coelacant1/SigmaProtogen/BetaProtogen/Pictures/20210629_173443.jpg

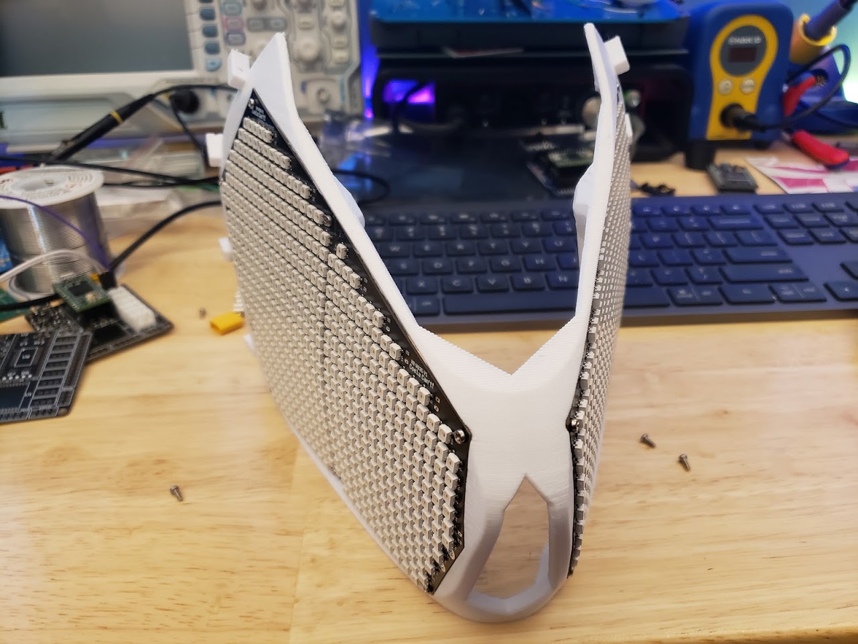
BetaProtogen/Pictures/20210629_173443.jpg
