coelacant1/SigmaProtogen/BetaProtogen/Pictures/BottomLayer.png

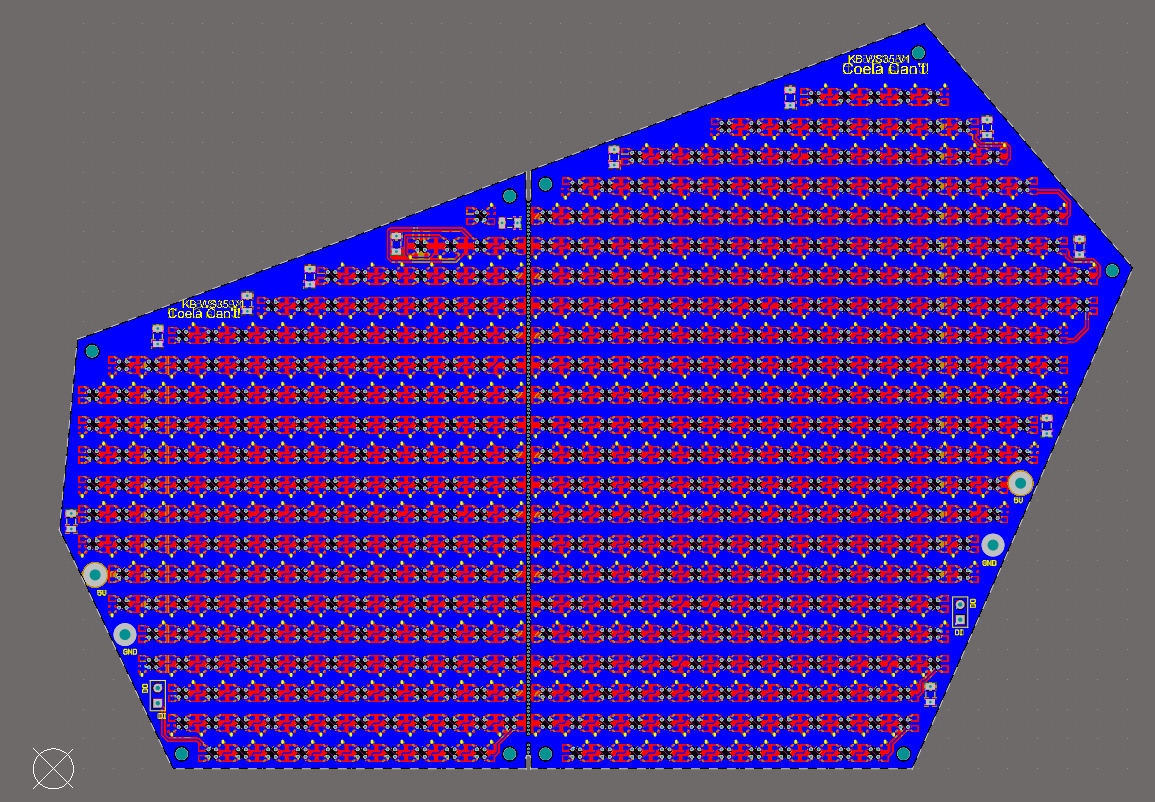
BetaProtogen/Pictures/BottomLayer.png
