coelacant1/SigmaProtogen/BetaProtogen/Pictures/CoelaProtoPublicV1_WS35_blank.png

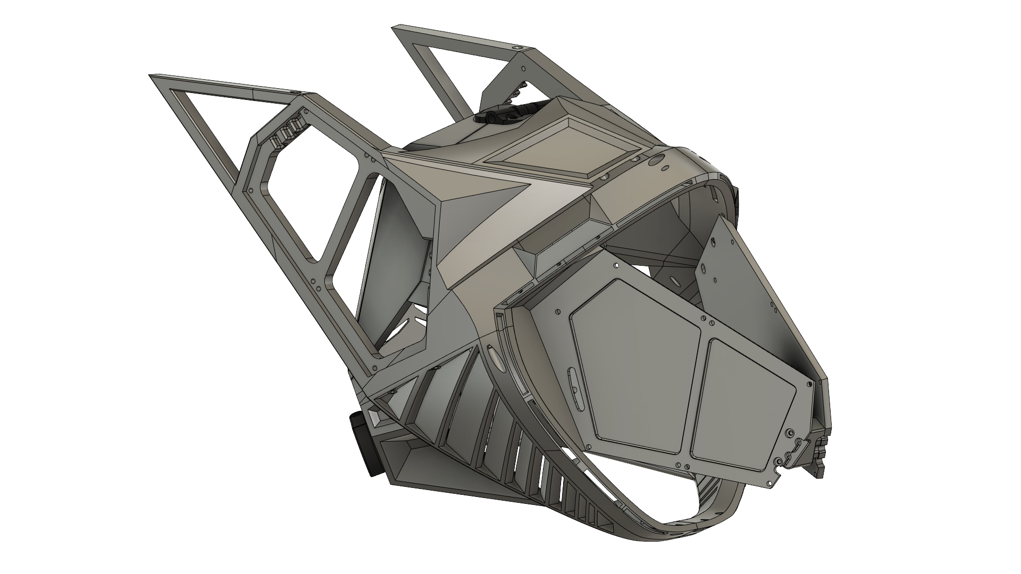
BetaProtogen/Pictures/CoelaProtoPublicV1_WS35_blank.png
