coelacant1/SigmaProtogen/BetaProtogen/Pictures/CoelaProtoPublicV1_WS35_Bottom.png

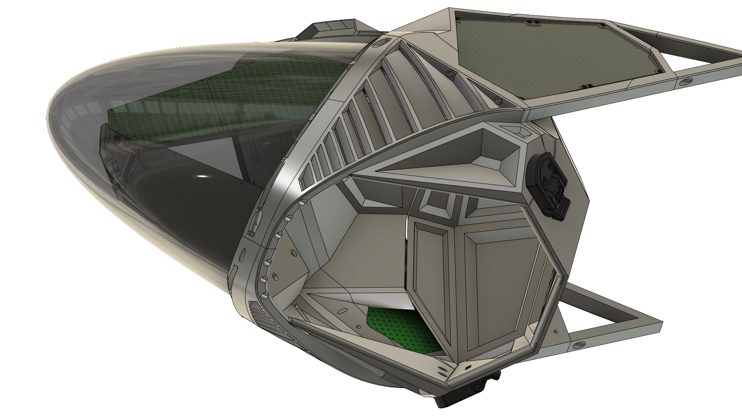
BetaProtogen/Pictures/CoelaProtoPublicV1_WS35_Bottom.png
