coelacant1/SigmaProtogen/BetaProtogen/Pictures/CoelaProtoPublicV1_WS35_Full.png

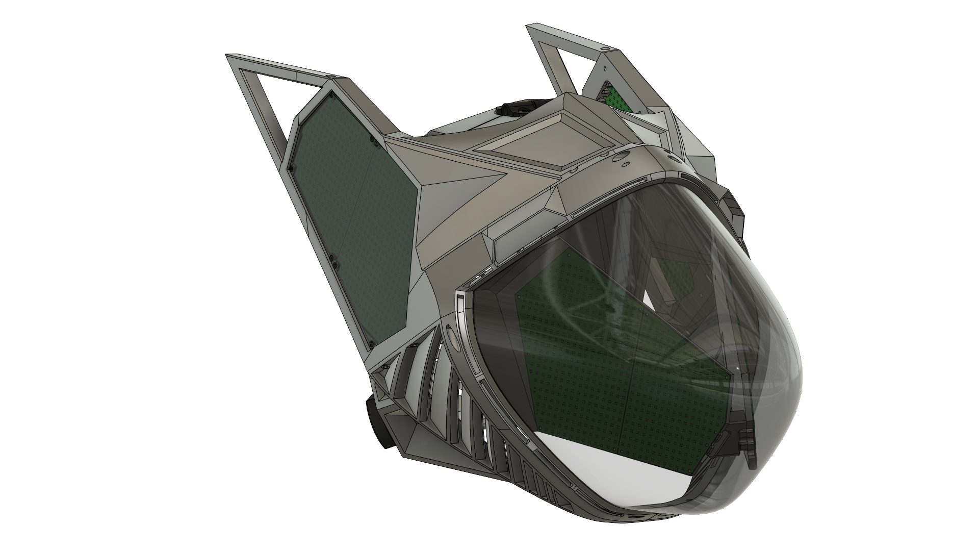
BetaProtogen/Pictures/CoelaProtoPublicV1_WS35_Full.png
