coelacant1/SigmaProtogen/BetaProtogen/Pictures/CoelaProtoPublicV1_WS35_Open.png

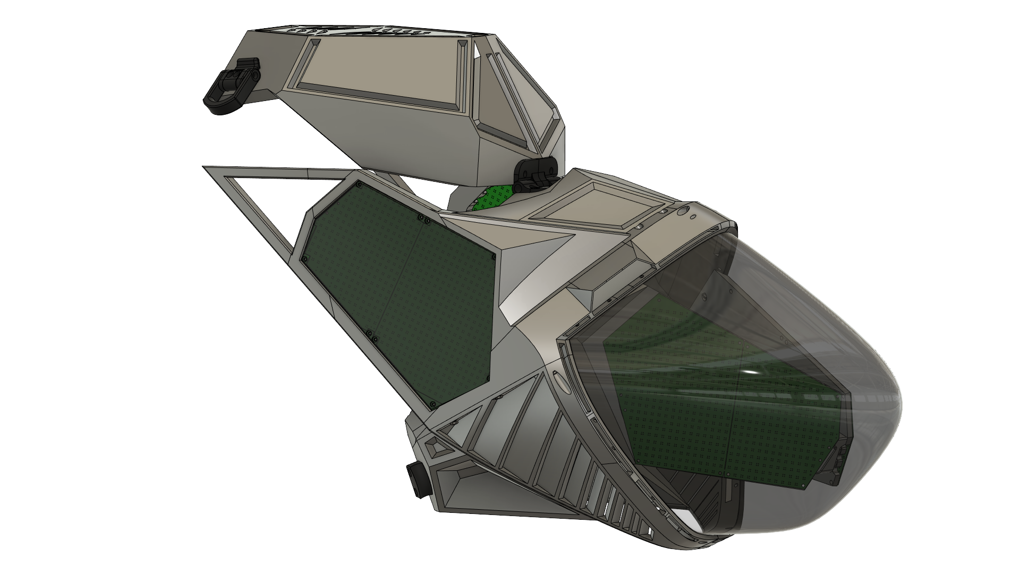
BetaProtogen/Pictures/CoelaProtoPublicV1_WS35_Open.png
