coelacant1/SigmaProtogen/BetaProtogen/Pictures/CoelaProtoPublicV1_WS35_OpenBack.png

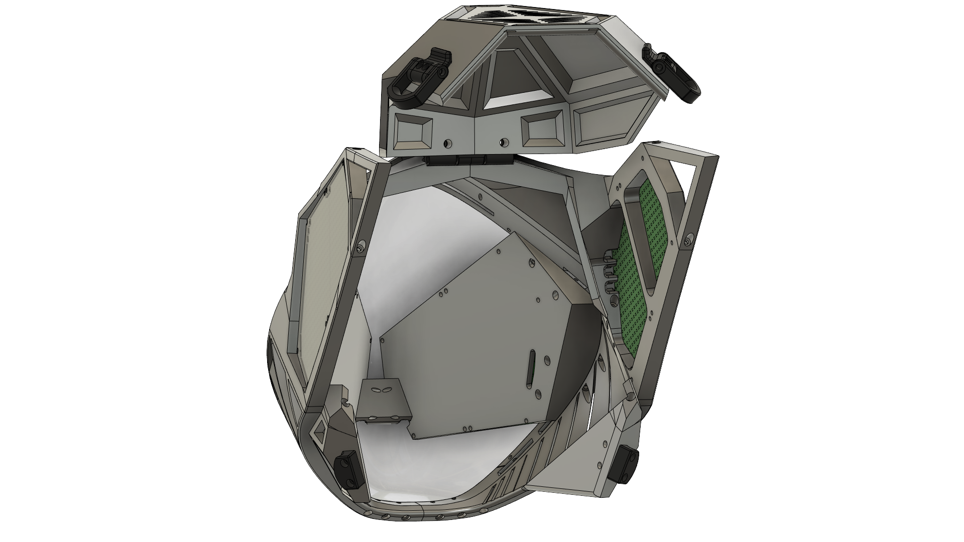
BetaProtogen/Pictures/CoelaProtoPublicV1_WS35_OpenBack.png
