coelacant1/SigmaProtogen/BetaProtogen/Pictures/E_W8pO6XIAAdrPj.jpg

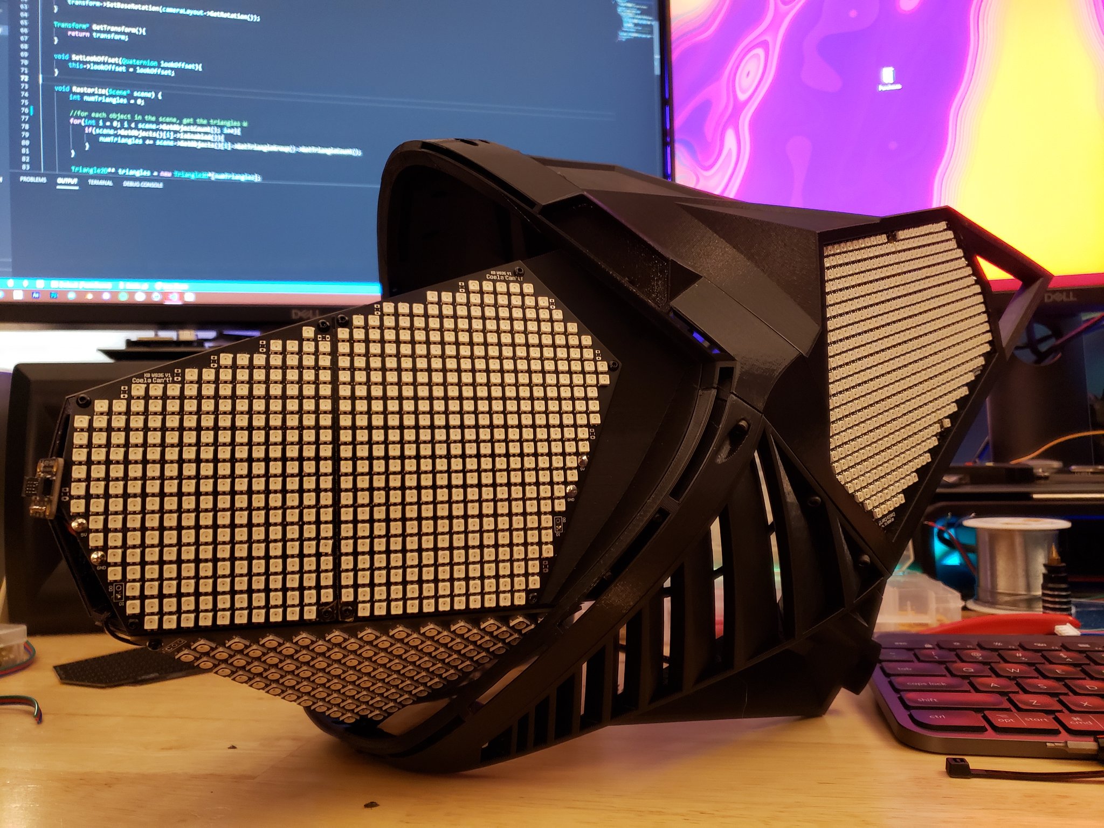
BetaProtogen/Pictures/E_W8pO6XIAAdrPj.jpg
