coelacant1/SigmaProtogen/BetaProtogen/Pictures/FullHead.png

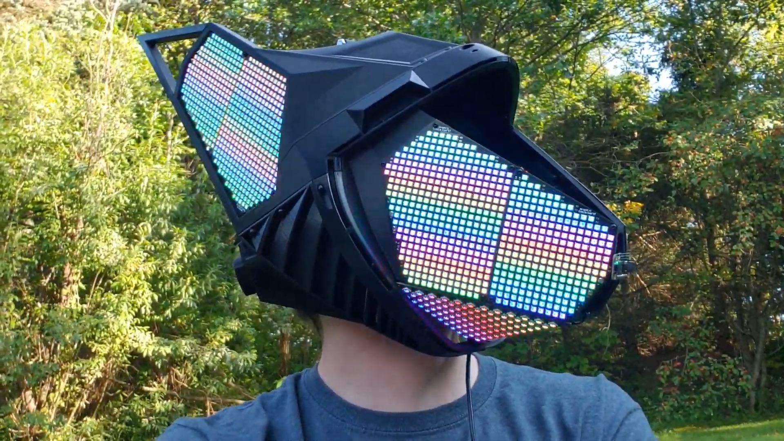
BetaProtogen/Pictures/FullHead.png
