coelacant1/SigmaProtogen/BetaProtogen/Pictures/LED.png

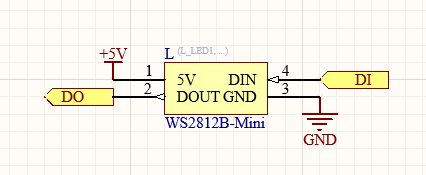
BetaProtogen/Pictures/LED.png
