coelacant1/SigmaProtogen/BetaProtogen/Pictures/LEDBoard1.png

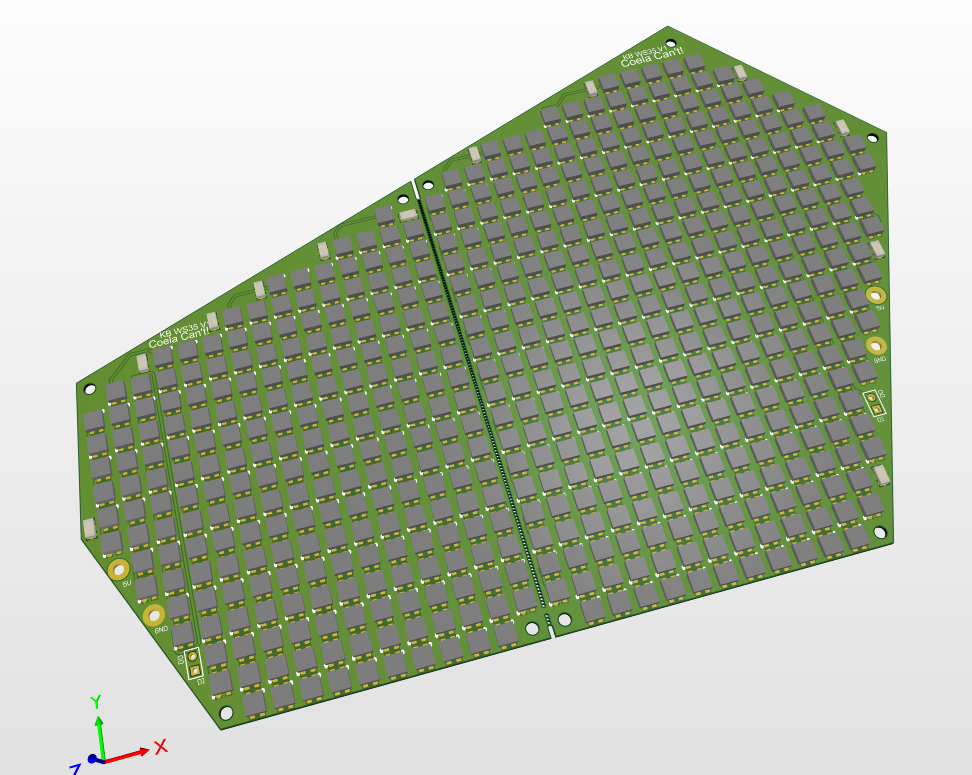
BetaProtogen/Pictures/LEDBoard1.png
