coelacant1/SigmaProtogen/BetaProtogen/Pictures/SignalLayer1.png

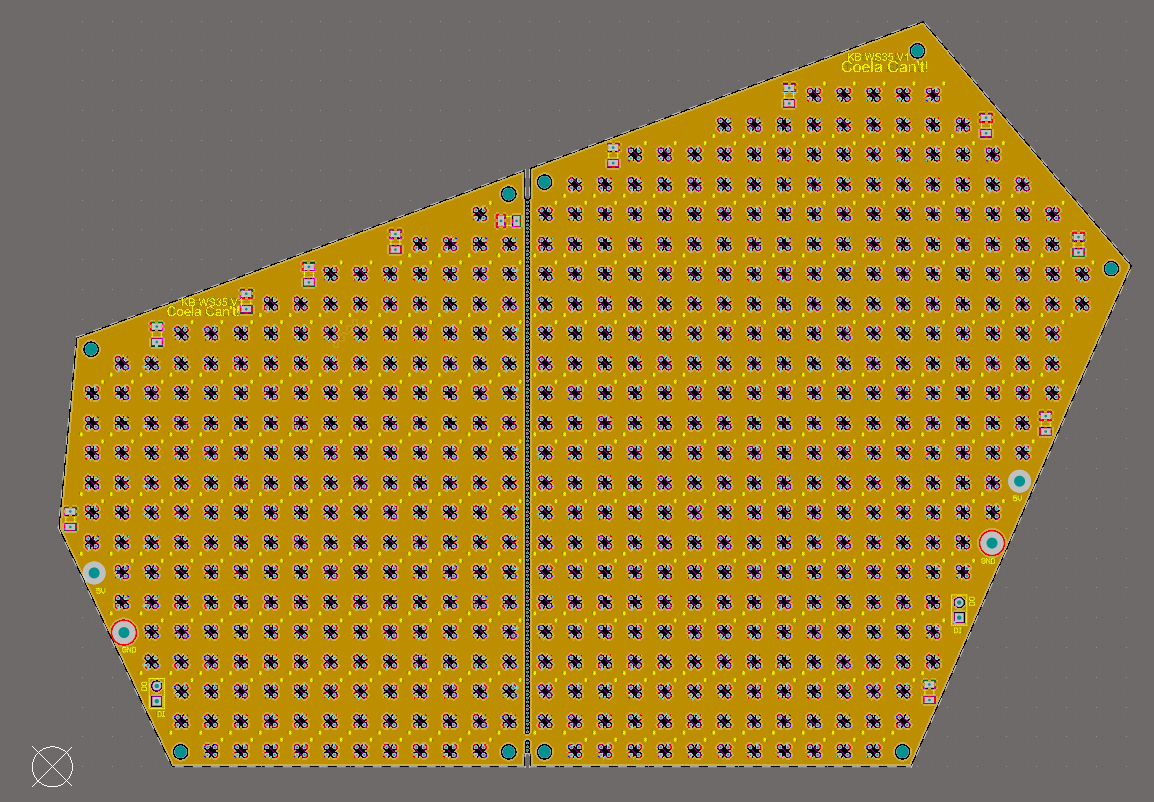
BetaProtogen/Pictures/SignalLayer1.png
