coelacant1/SigmaProtogen/BetaProtogen/Pictures/SignalLayer2.png

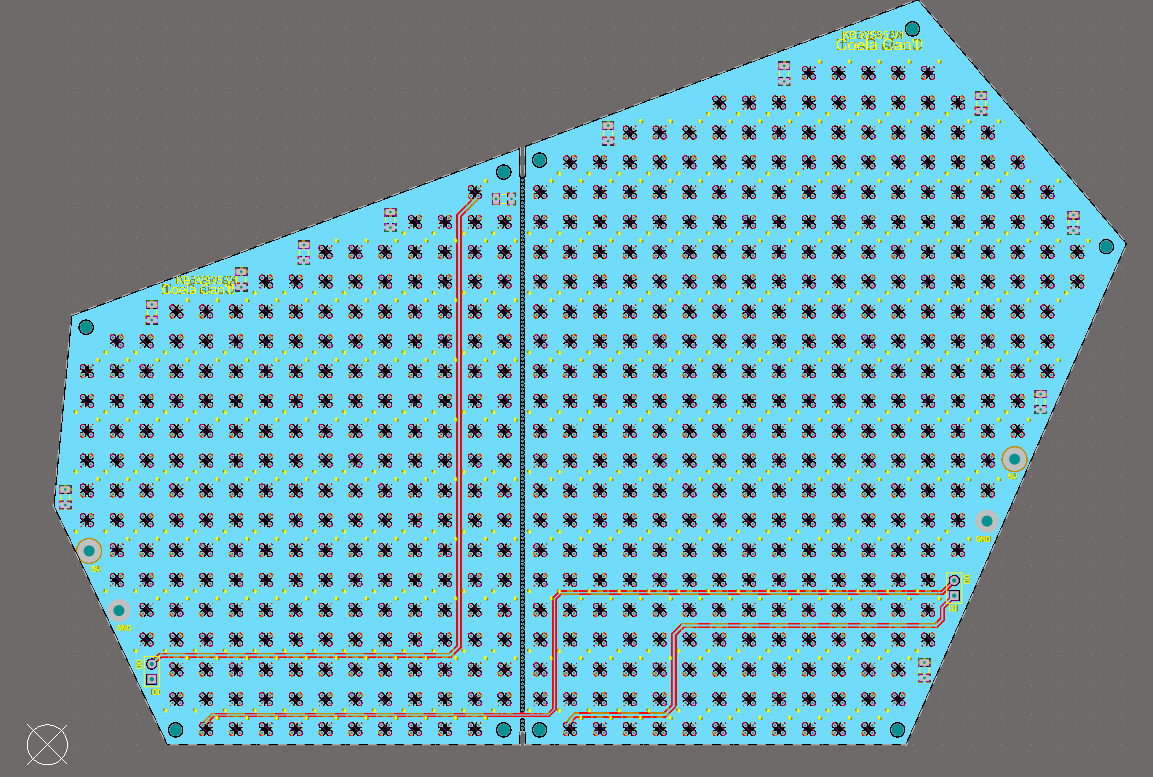
BetaProtogen/Pictures/SignalLayer2.png
