coelacant1/SigmaProtogen/BetaProtogen/Pictures/Thumbnail.png

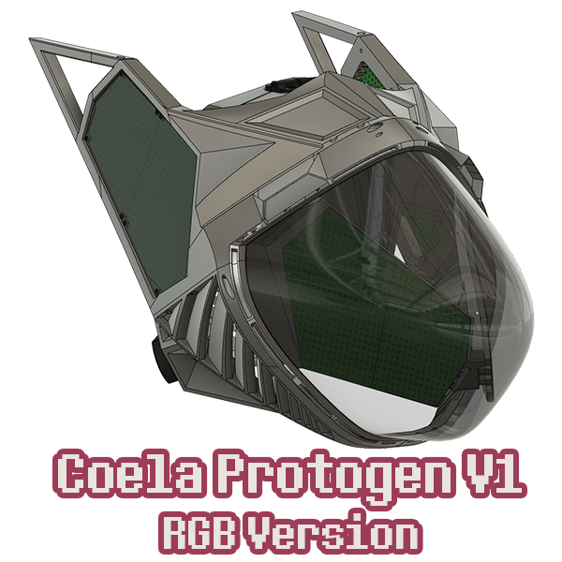
BetaProtogen/Pictures/Thumbnail.png
