coelacant1/SigmaProtogen/BetaProtogen/Pictures/TopCopper.png

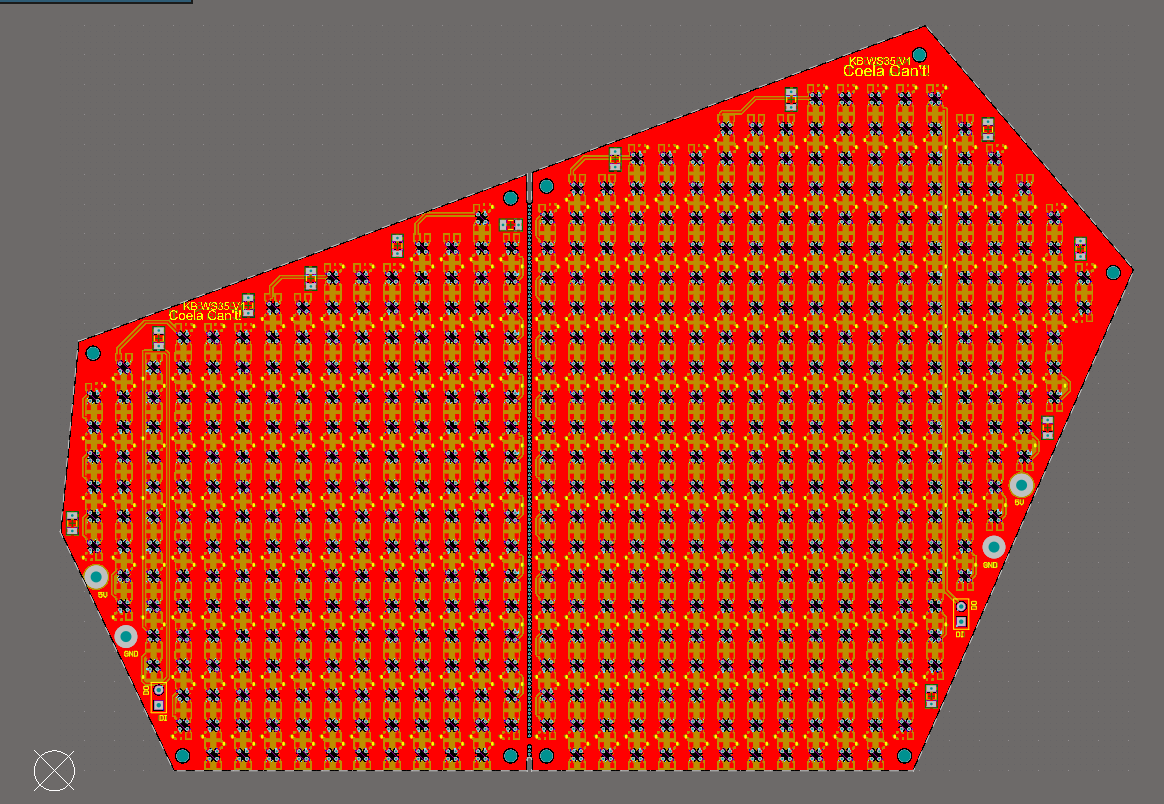
BetaProtogen/Pictures/TopCopper.png
