coelacant1/SigmaProtogen/DeltaProtogen/Pictures/CoelaProtoSmoothV1_MAX7219.png

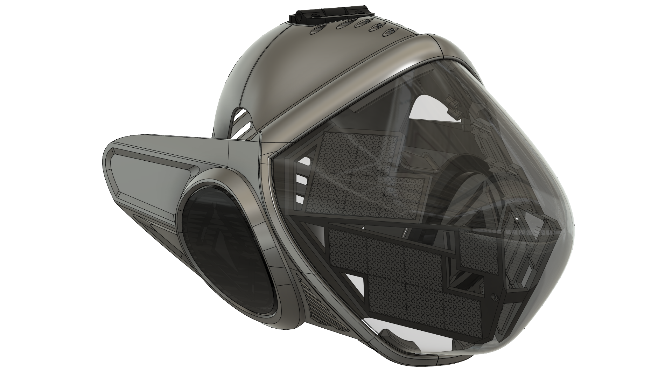
DeltaProtogen/Pictures/CoelaProtoSmoothV1_MAX7219.png
