coelacant1/SigmaProtogen/DeltaProtogen/Pictures/CoelaProtoSmoothV1_P3Back.png

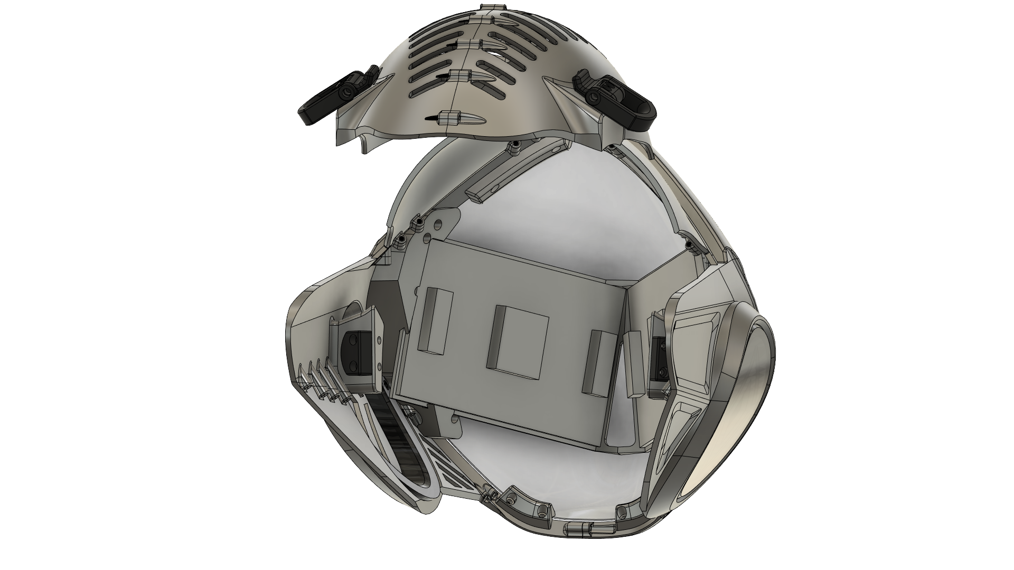
DeltaProtogen/Pictures/CoelaProtoSmoothV1_P3Back.png
