coelacant1/SigmaProtogen/DeltaProtogen/Pictures/CoelaProtoSmoothV1_WS35 P3.png

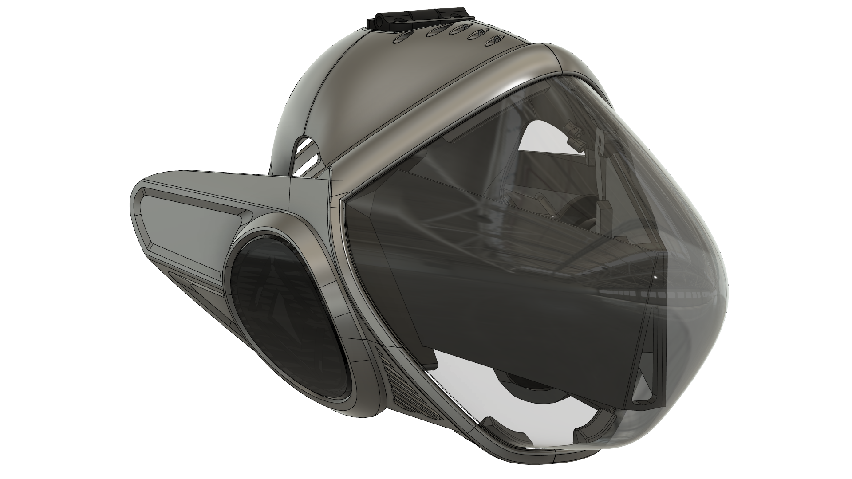
DeltaProtogen/Pictures/CoelaProtoSmoothV1_WS35 P3.png
