coelacant1/SigmaProtogen/DeltaProtogen/Pictures/CoelaProtoSmoothV1_WS35Back.png

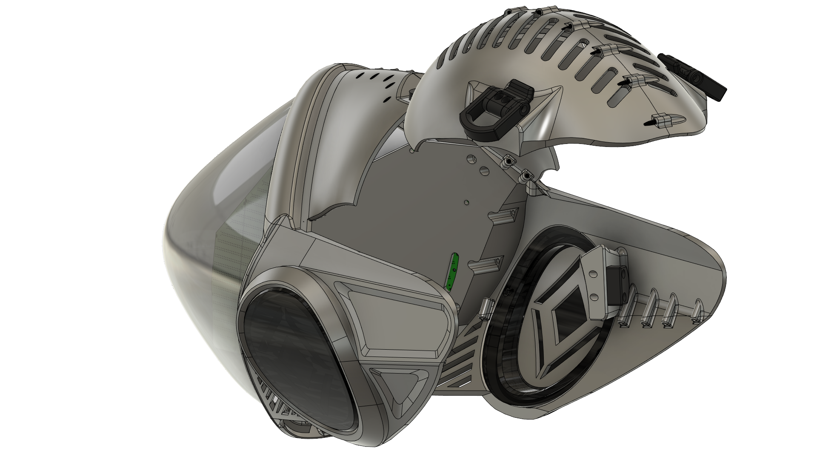
DeltaProtogen/Pictures/CoelaProtoSmoothV1_WS35Back.png
