coelacant1/SigmaProtogen/DeltaProtogen/Pictures/Delta Protogen V1.png

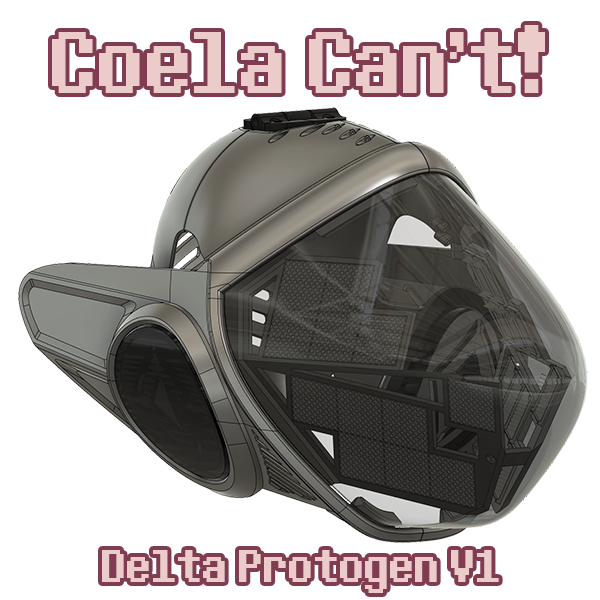
DeltaProtogen/Pictures/Delta Protogen V1.png
