coelacant1/SigmaProtogen/DeltaProtogen/Pictures/XRay.jpg

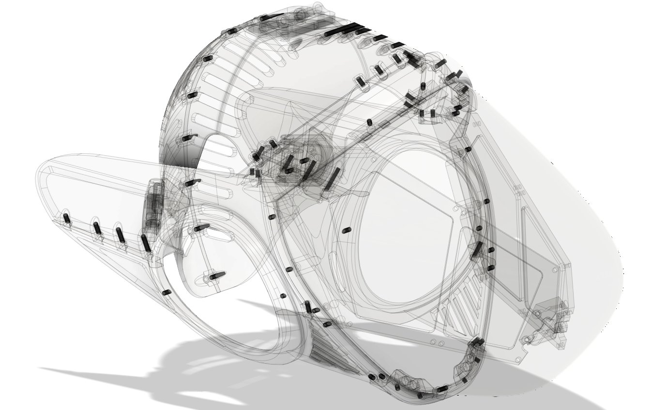
DeltaProtogen/Pictures/XRay.jpg
