coelacant1/SigmaProtogen/EpsilonProtogen/Pictures/1 (1).jpg

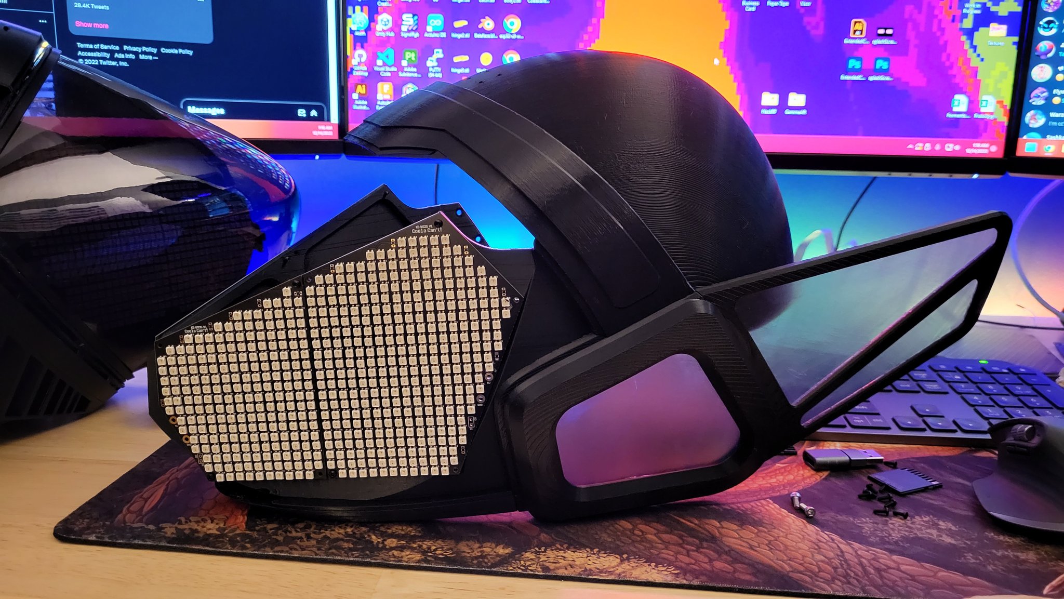
EpsilonProtogen/Pictures/1 (1).jpg
