coelacant1/SigmaProtogen/EpsilonProtogen/Pictures/1 (2).jpg

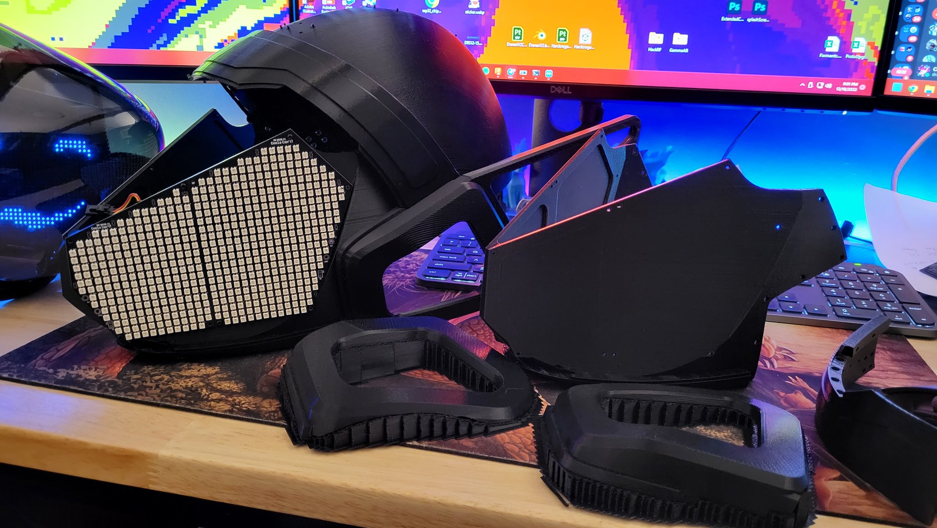
EpsilonProtogen/Pictures/1 (2).jpg
