coelacant1/SigmaProtogen/EpsilonProtogen/Pictures/1 (3).jpg

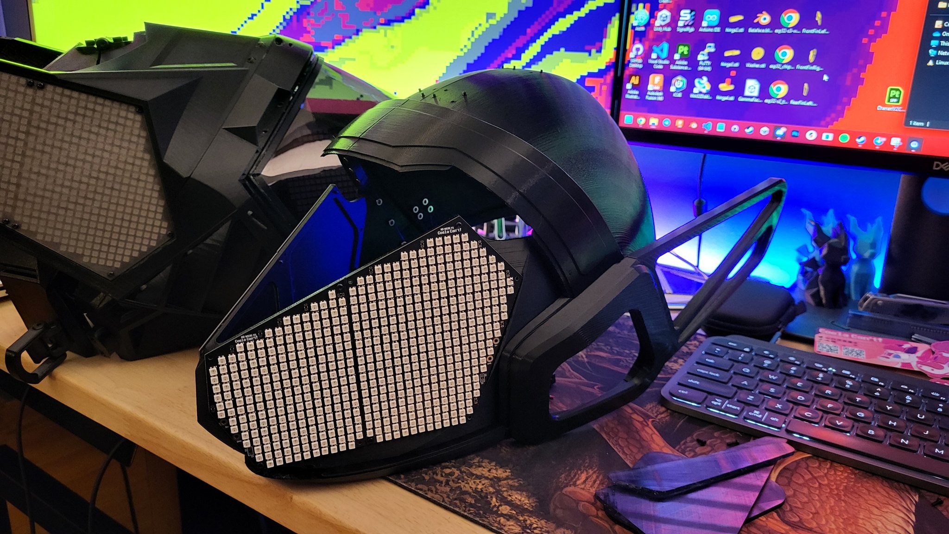
EpsilonProtogen/Pictures/1 (3).jpg
