coelacant1/SigmaProtogen/EpsilonProtogen/Pictures/1 (4).jpg

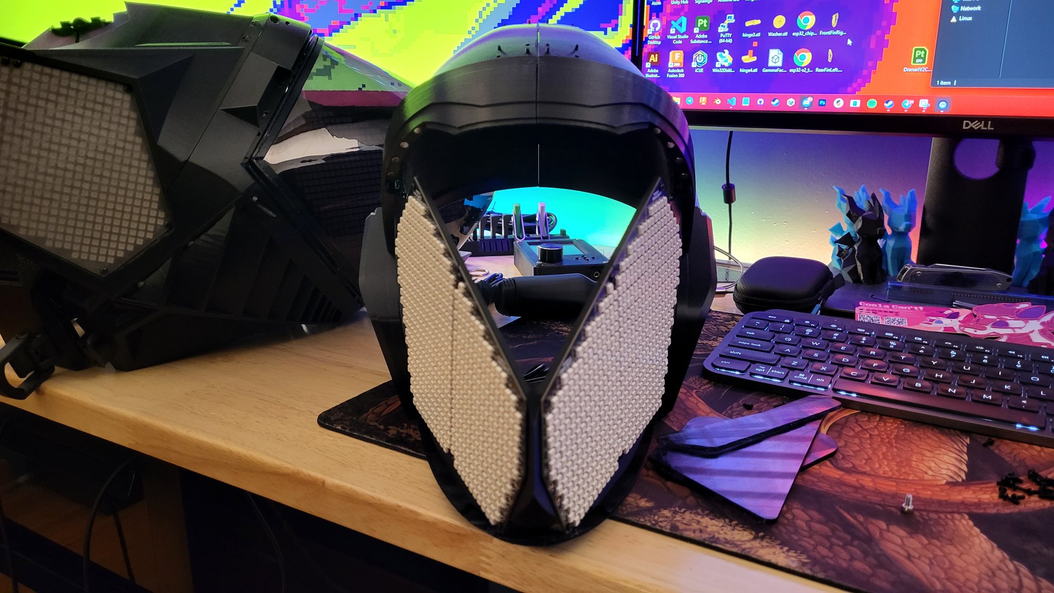
EpsilonProtogen/Pictures/1 (4).jpg
