coelacant1/SigmaProtogen/EpsilonProtogen/Pictures/Back.png

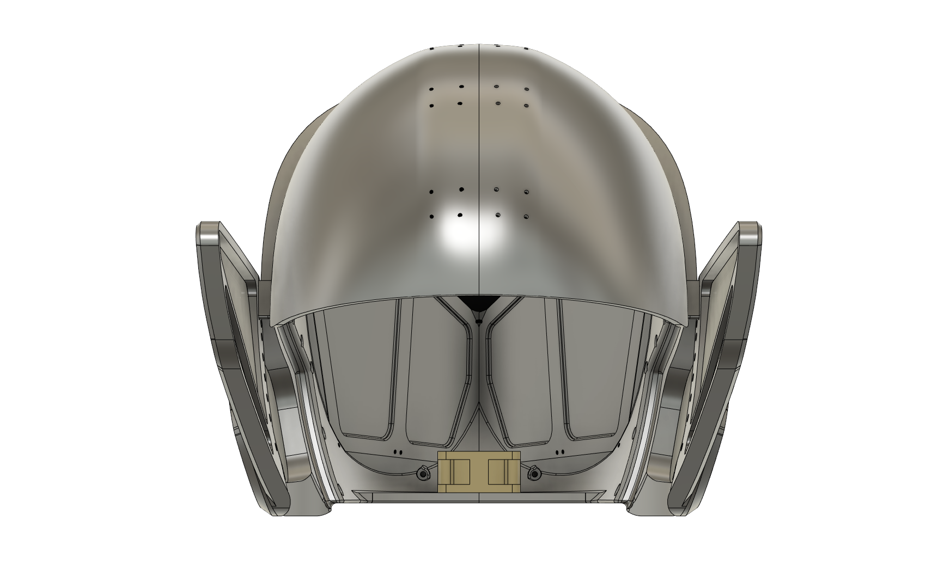
EpsilonProtogen/Pictures/Back.png
