coelacant1/SigmaProtogen/EpsilonProtogen/Pictures/Bottom.png

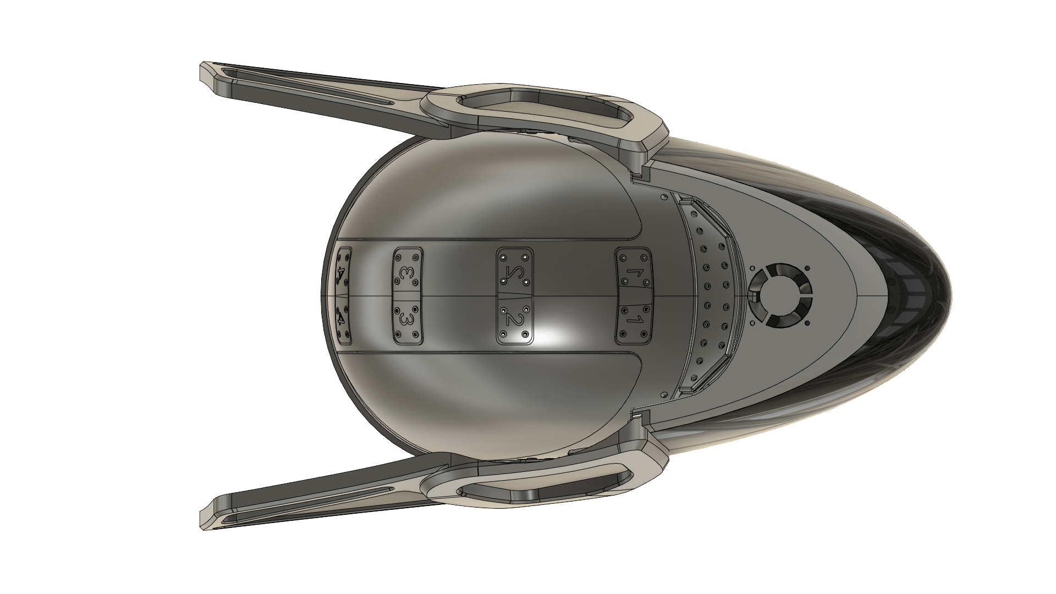
EpsilonProtogen/Pictures/Bottom.png
