coelacant1/SigmaProtogen/EpsilonProtogen/Pictures/Edges.png

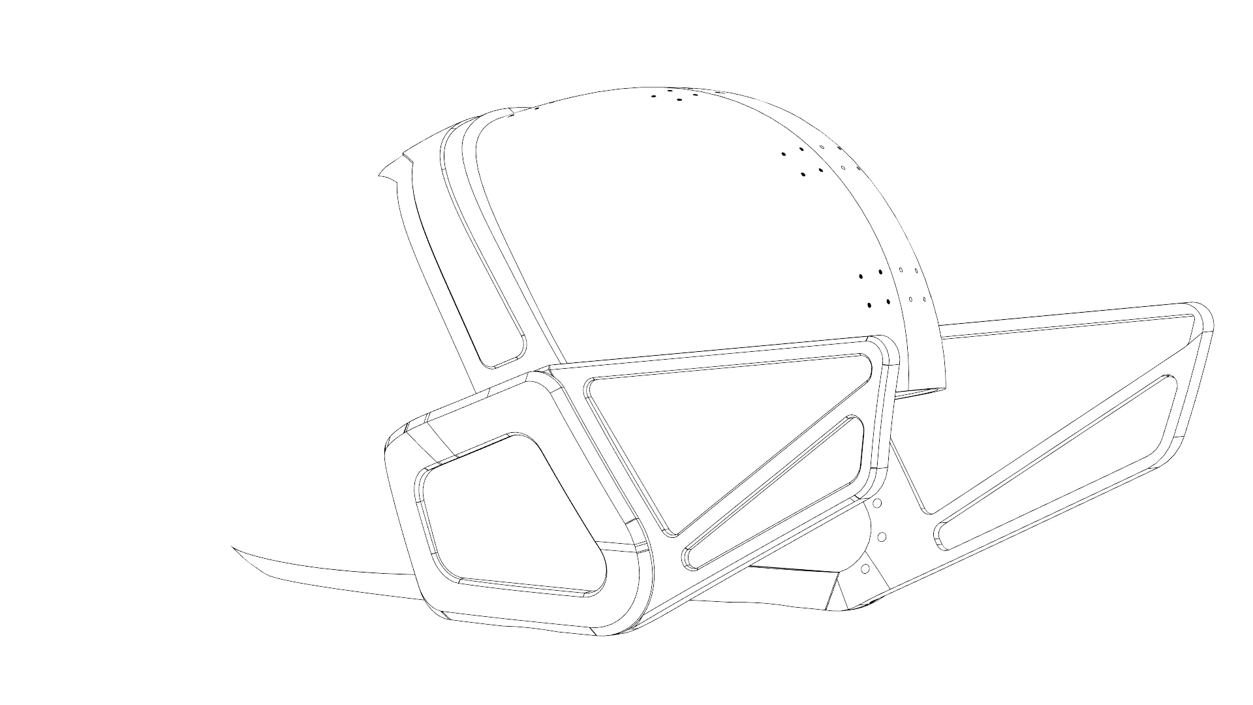
EpsilonProtogen/Pictures/Edges.png
