coelacant1/SigmaProtogen/EpsilonProtogen/Pictures/Full.png

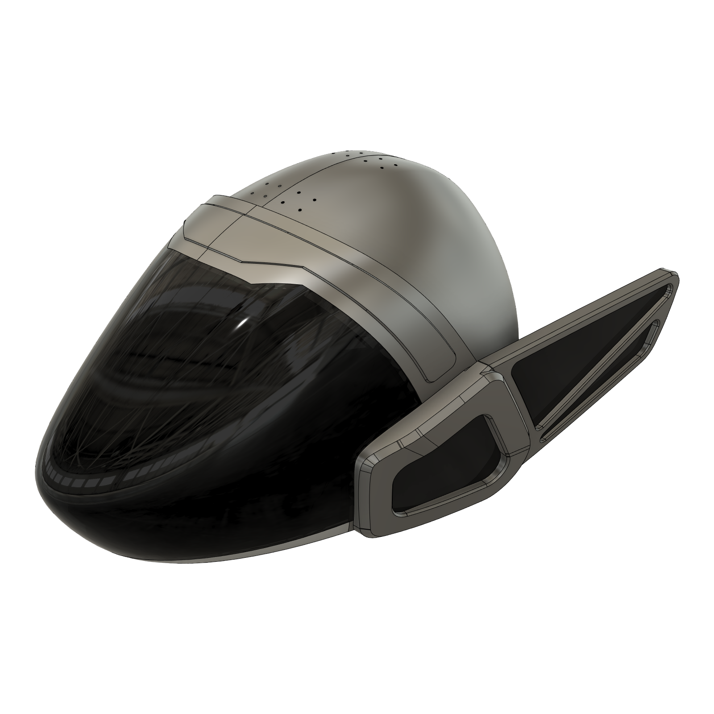
EpsilonProtogen/Pictures/Full.png
