coelacant1/SigmaProtogen/EpsilonProtogen/Pictures/FullPlatter.png

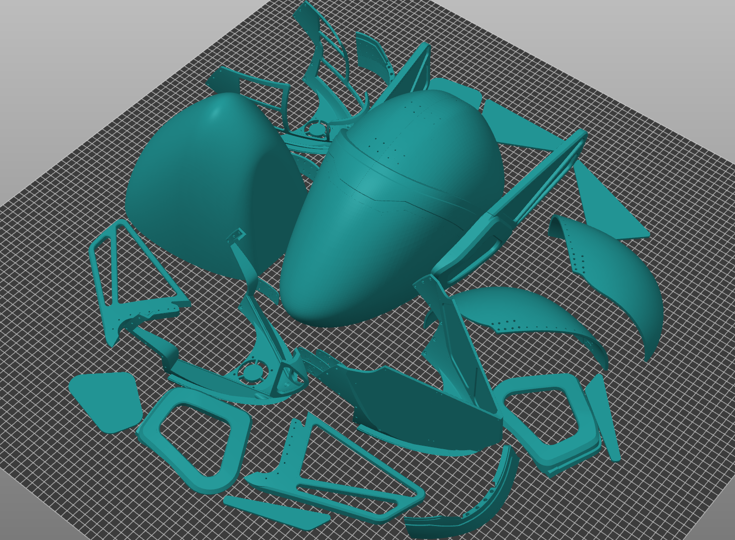
EpsilonProtogen/Pictures/FullPlatter.png
