coelacant1/SigmaProtogen/EpsilonProtogen/Pictures/HUB75.png

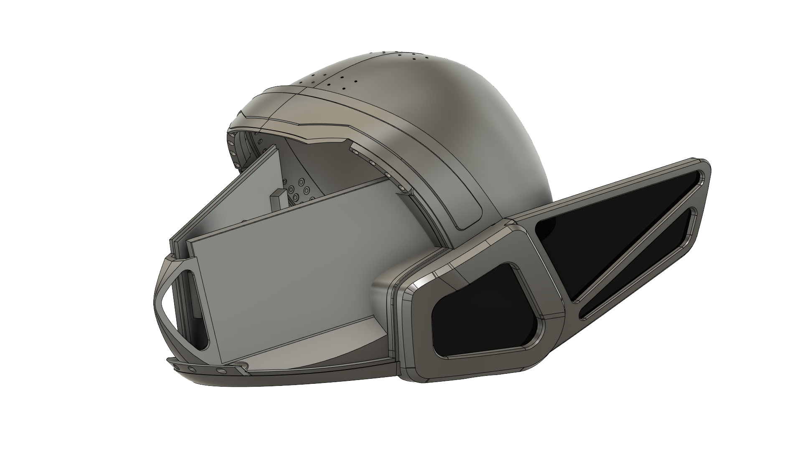
EpsilonProtogen/Pictures/HUB75.png
