coelacant1/SigmaProtogen/EpsilonProtogen/Pictures/MAX7219.png

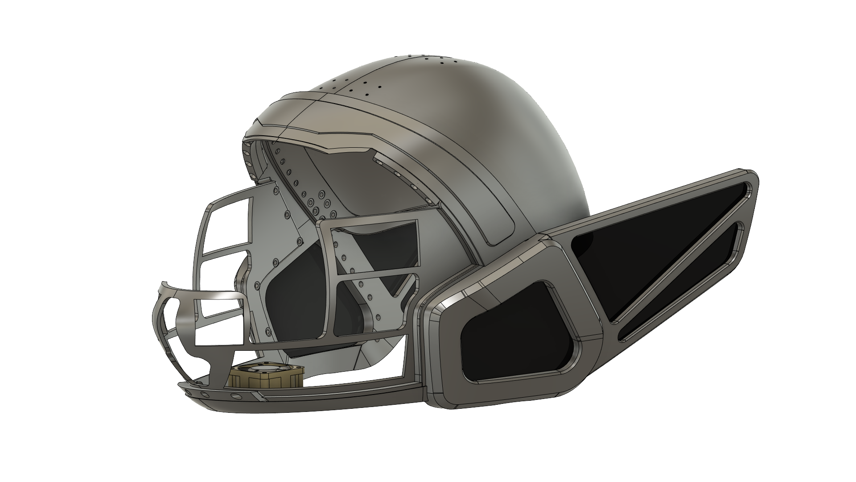
EpsilonProtogen/Pictures/MAX7219.png
