coelacant1/SigmaProtogen/EpsilonProtogen/Pictures/VacuumBuck.png

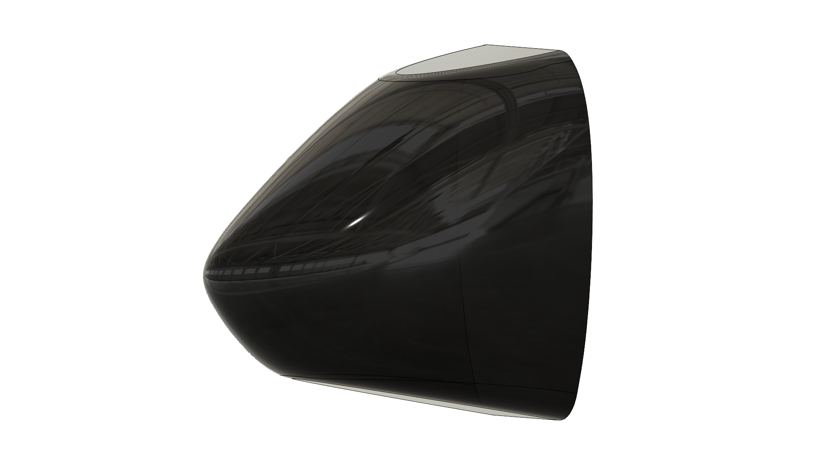
EpsilonProtogen/Pictures/VacuumBuck.png
