coelacant1/SigmaProtogen/SigmaProtogen/Pictures/HUB75.png

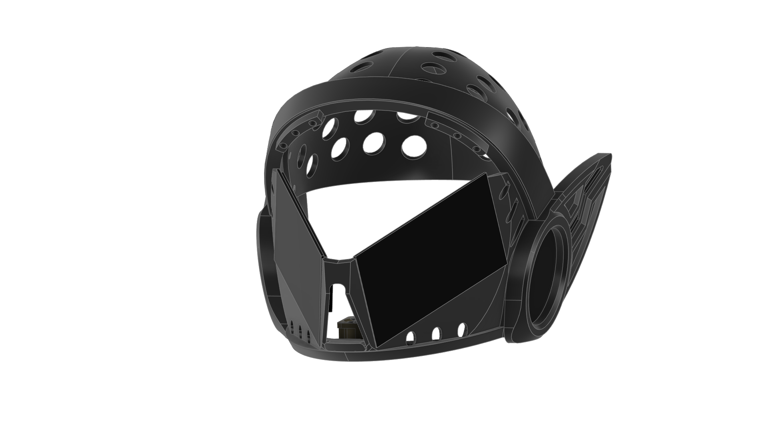
SigmaProtogen/Pictures/HUB75.png
