coelacant1/SigmaProtogen/SigmaProtogen/Pictures/SigmaAll.png

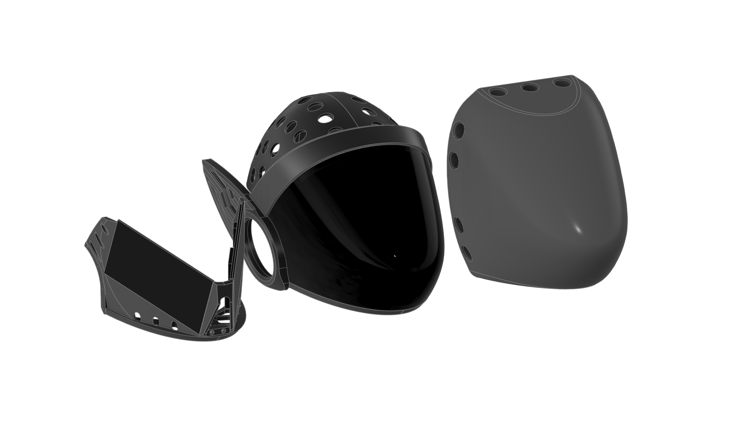
SigmaProtogen/Pictures/SigmaAll.png
