coelacant1/SigmaProtogen/SigmaProtogen/Pictures/SigmaBottom.png

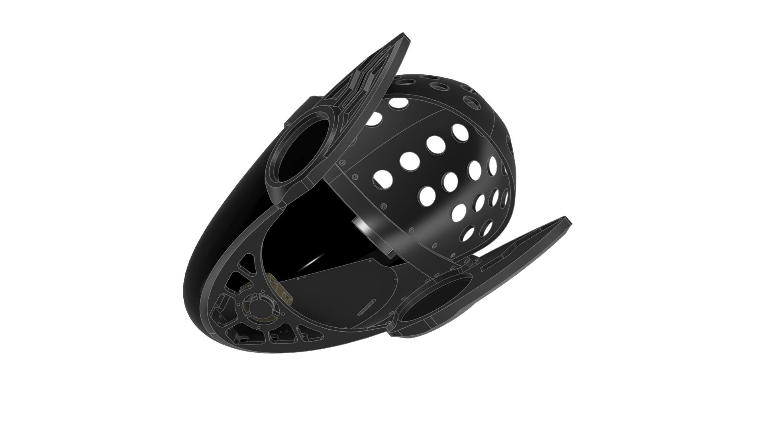
SigmaProtogen/Pictures/SigmaBottom.png
