coelacant1/SigmaProtogen/SigmaProtogen/Pictures/SigmaFront.png

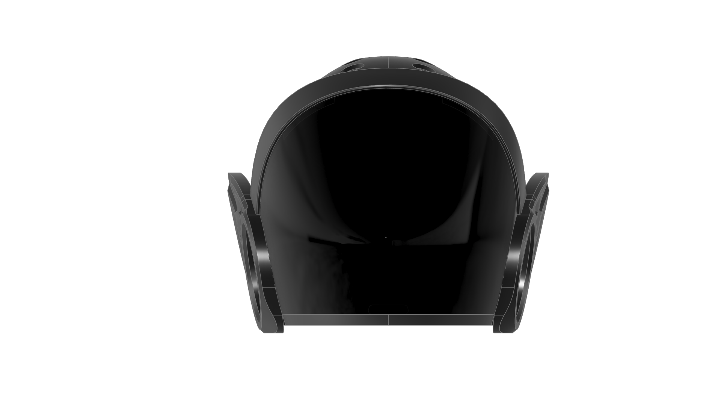
SigmaProtogen/Pictures/SigmaFront.png
