coelacant1/SigmaProtogen/SigmaProtogen/Pictures/SigmaQuarter.png

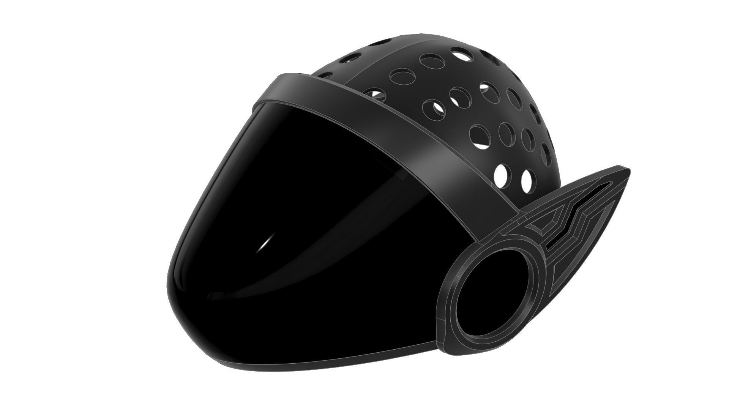
SigmaProtogen/Pictures/SigmaQuarter.png
