coelacant1/SigmaProtogen/SigmaProtogen/Pictures/SigmaSide.png

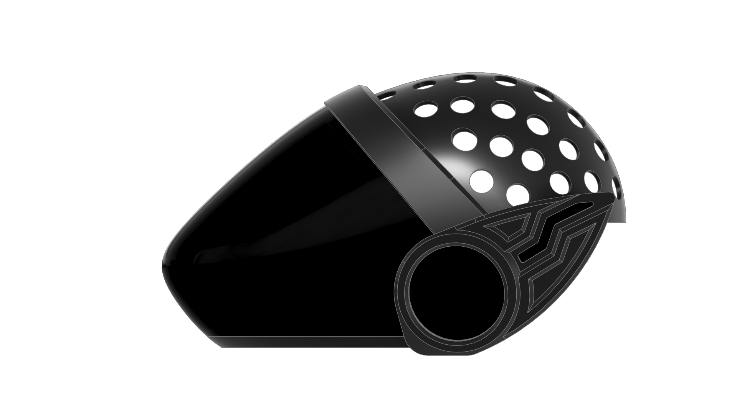
SigmaProtogen/Pictures/SigmaSide.png
