coelacant1/SigmaProtogen/SigmaProtogen/Pictures/SigmaThumbnail.png

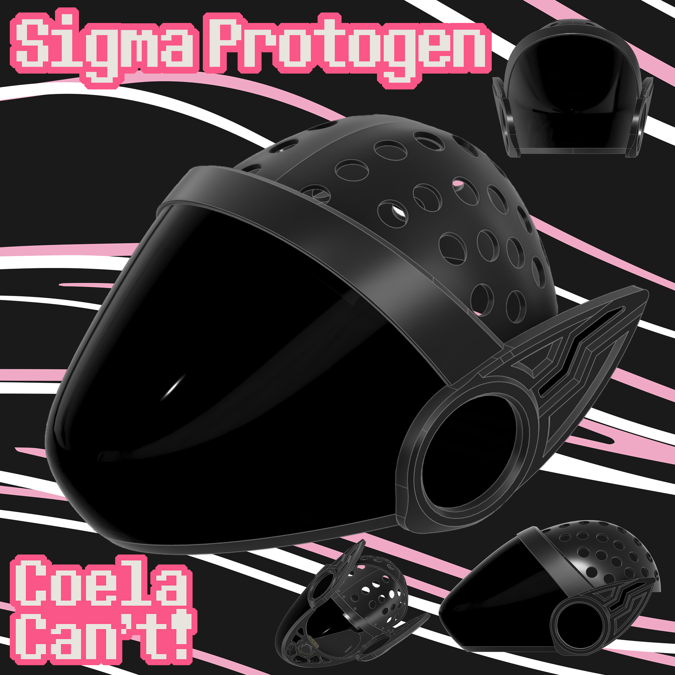
SigmaProtogen/Pictures/SigmaThumbnail.png
