coelacant1/SigmaProtogen/DeltaProtogen/Latch/LatchOuterRotateWider_V1-0.stl

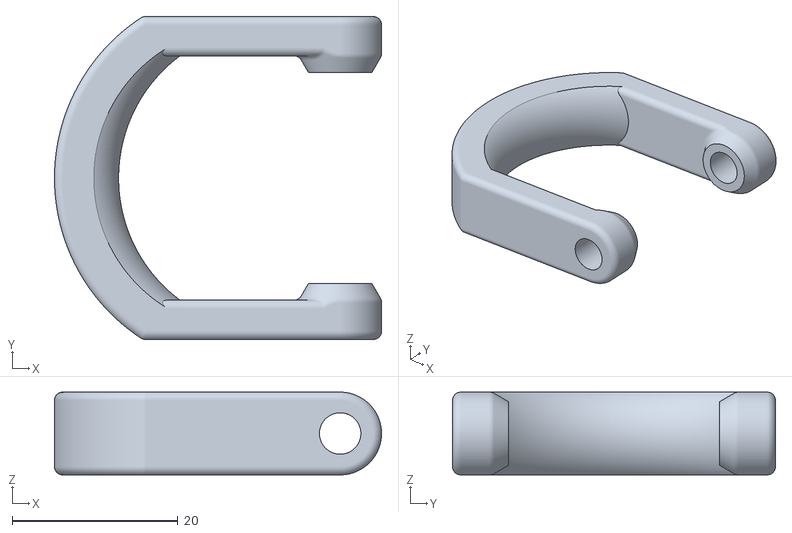
[picture p61: CAD file, 2025-01-01]
DeltaProtogen/Latch/LatchOuterRotateWider_V1-0.stl
39.5 x 39.0 x 10.0
