coelacant1/SigmaProtogen/DeltaProtogen/LED Mount KS W35/KSWS35_Left_V1-0.stl

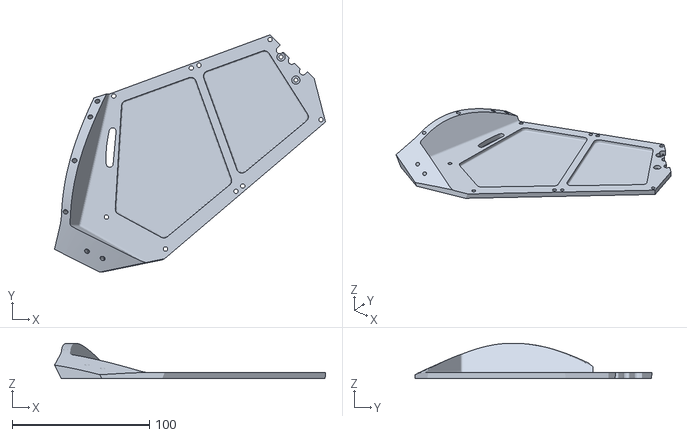
[picture p62: CAD file, 2025-01-01]
DeltaProtogen/LED Mount KS W35/KSWS35_Left_V1-0.stl
197.3 x 172.9 x 25.8
