coelacant1/SigmaProtogen/DeltaProtogen/LED Mount MAX7219/MAX7219BotRight_V1-0.stl

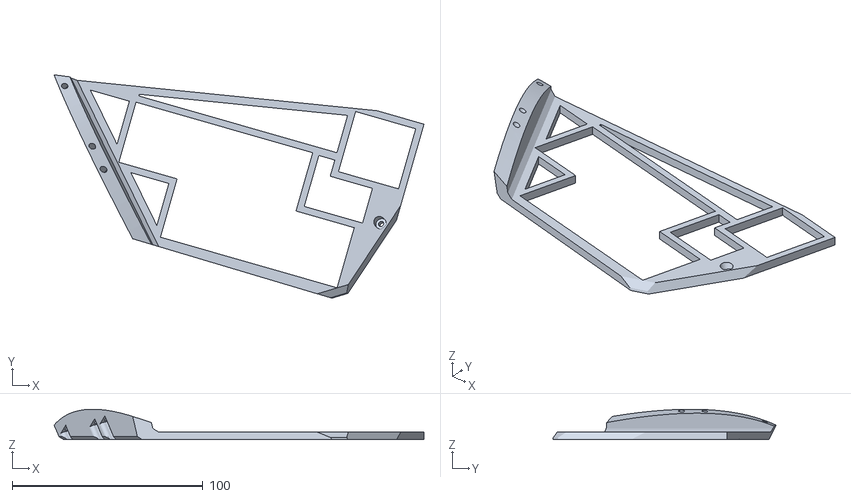
[picture p63: CAD file, 2025-01-01]
DeltaProtogen/LED Mount MAX7219/MAX7219BotRight_V1-0.stl
194.1 x 117.2 x 16.0
