coelacant1/SigmaProtogen/DeltaProtogen/LED Mount P3 HUB75/P3LeftMount_V1-0.stl

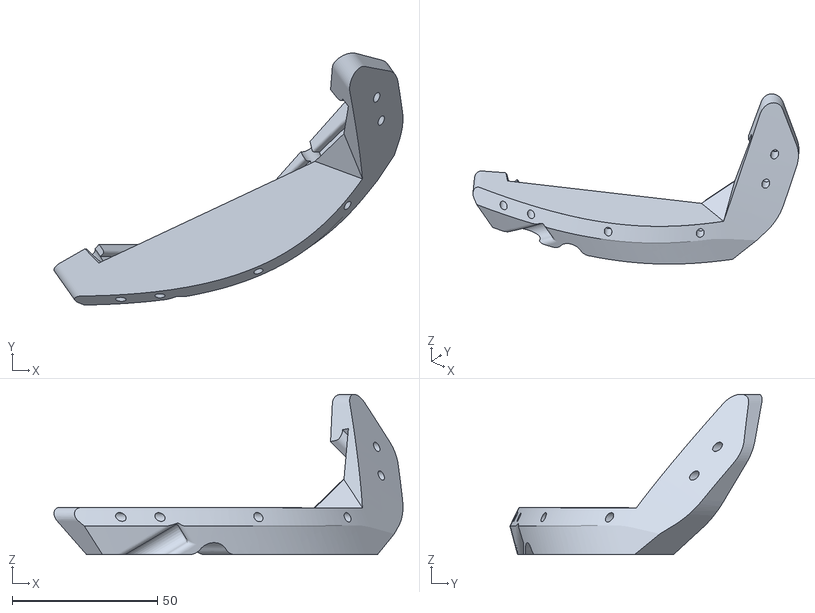
[picture p64: CAD file, 2025-01-01]
DeltaProtogen/LED Mount P3 HUB75/P3LeftMount_V1-0.stl
120.0 x 86.7 x 55.2
