coelacant1/SigmaProtogen/DeltaProtogen/Side Displays/RightPuckInnerSample_V1-0.stl

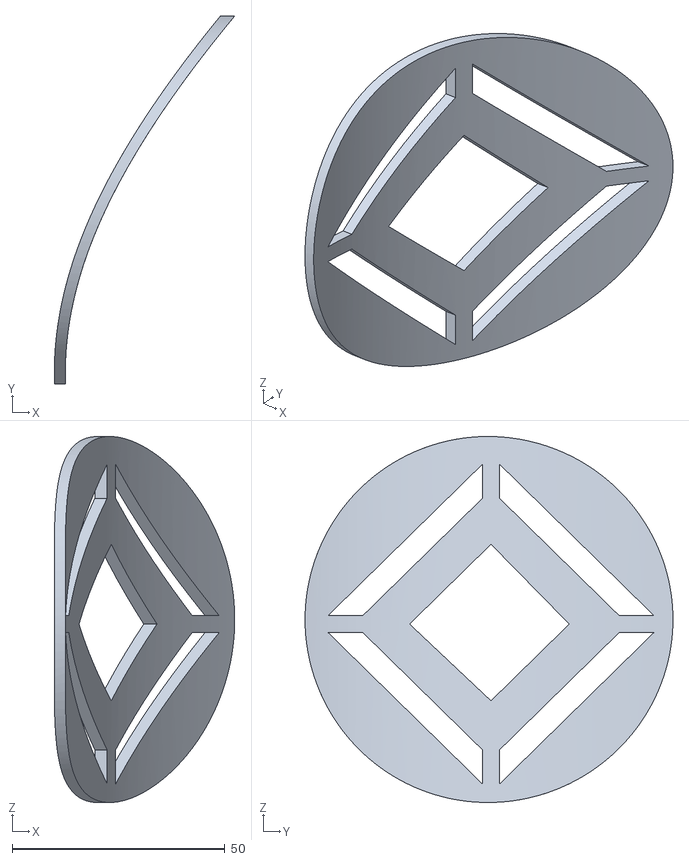
[picture p65: CAD file, 2025-01-01]
DeltaProtogen/Side Displays/RightPuckInnerSample_V1-0.stl
42.4 x 86.5 x 86.0
