coelacant1/SigmaProtogen/DeltaProtogen/Visor Mounts/TopLeftInner_V1-1.stl

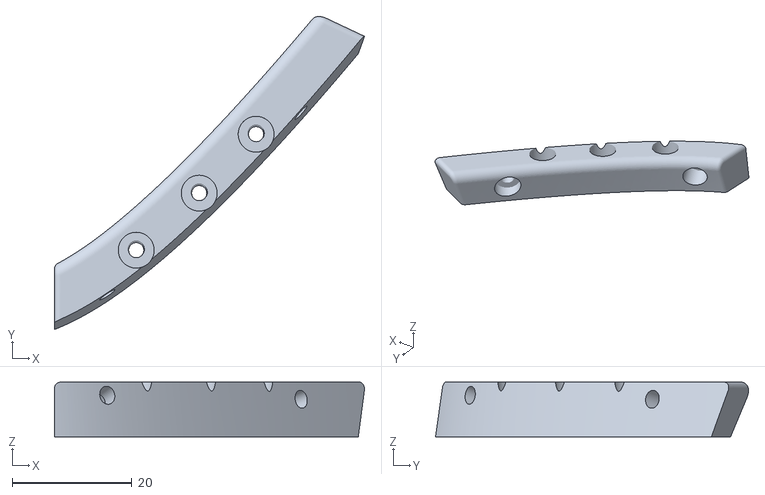
[picture p66: CAD file, 2025-01-01]
DeltaProtogen/Visor Mounts/TopLeftInner_V1-1.stl
51.8 x 52.3 x 9.16
