coelacant1/SigmaProtogen/DeltaProtogen/Visor/BuckBotLeft_V3-0.stl

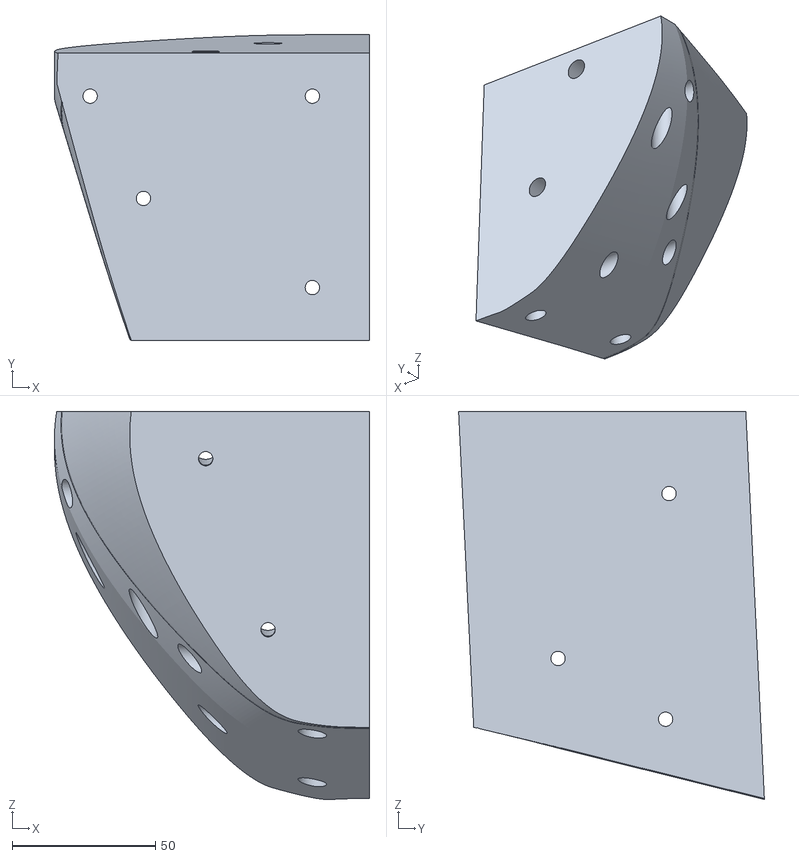
[picture p67: CAD file, 2025-01-01]
DeltaProtogen/Visor/BuckBotLeft_V3-0.stl
109.8 x 106.6 x 135.2
