coelacant1/SigmaProtogen/EpsilonProtogen/Frame Connectors/HelmetJoin4.stl

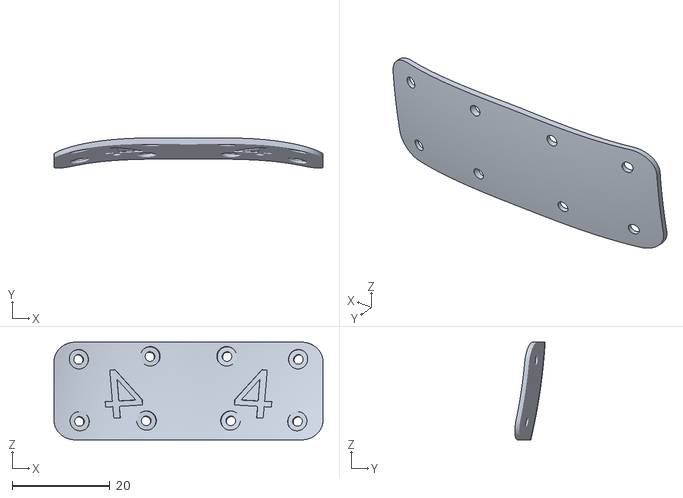
[picture p68: CAD file, 2025-01-01]
EpsilonProtogen/Frame Connectors/HelmetJoin4.stl
55.0 x 6.21 x 20.0
