coelacant1/SigmaProtogen/EpsilonProtogen/Frame/Left/RearTopFinDisplay.stl

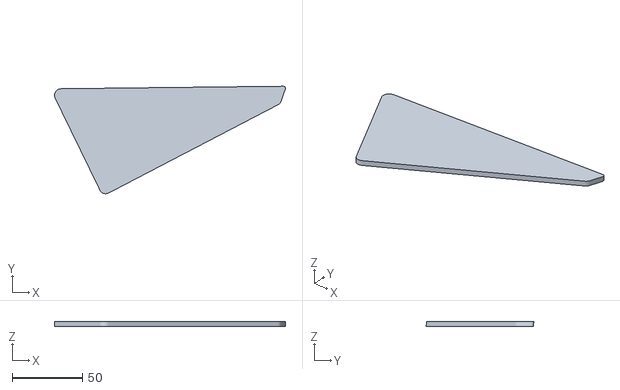
[picture p69: CAD file, 2025-01-01]
EpsilonProtogen/Frame/Left/RearTopFinDisplay.stl
164.5 x 76.6 x 3.29
