coelacant1/SigmaProtogen/EpsilonProtogen/Frame/Right/RearFinRight.stl

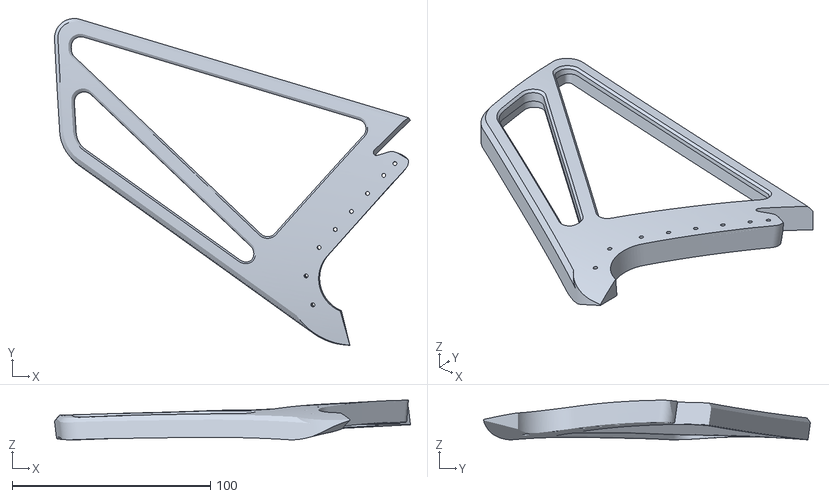
[picture p70: CAD file, 2025-01-01]
EpsilonProtogen/Frame/Right/RearFinRight.stl
179.5 x 164.9 x 20.0
