coelacant1/SigmaProtogen/EpsilonProtogen/HUB75/HUB75PanelReference.stl

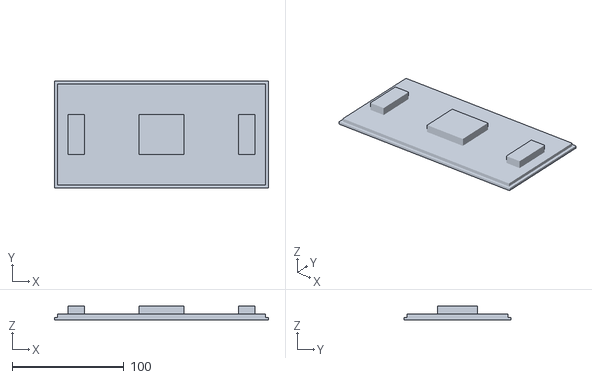
[picture p71: CAD file, 2025-01-01]
EpsilonProtogen/HUB75/HUB75PanelReference.stl
191.8 x 95.8 x 12.3
