coelacant1/SigmaProtogen/EpsilonProtogen/Visor/Mount/ForeheadTopLeft.stl

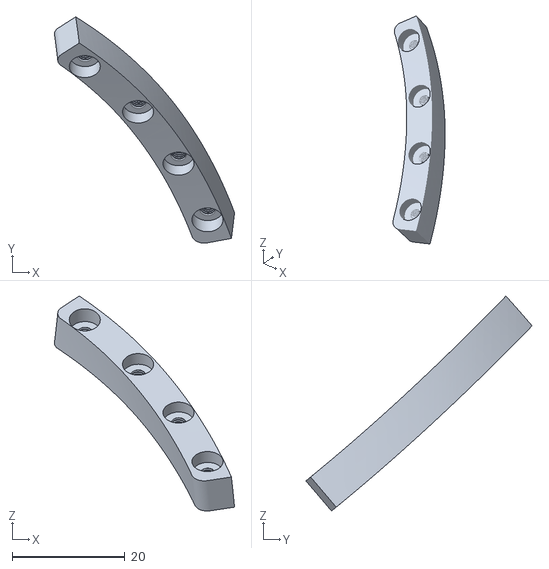
[picture p72: CAD file, 2025-01-01]
EpsilonProtogen/Visor/Mount/ForeheadTopLeft.stl
31.9 x 40.1 x 38.1
