coelacant1/SigmaProtogen/EpsilonProtogen/Visor/Visor.stl

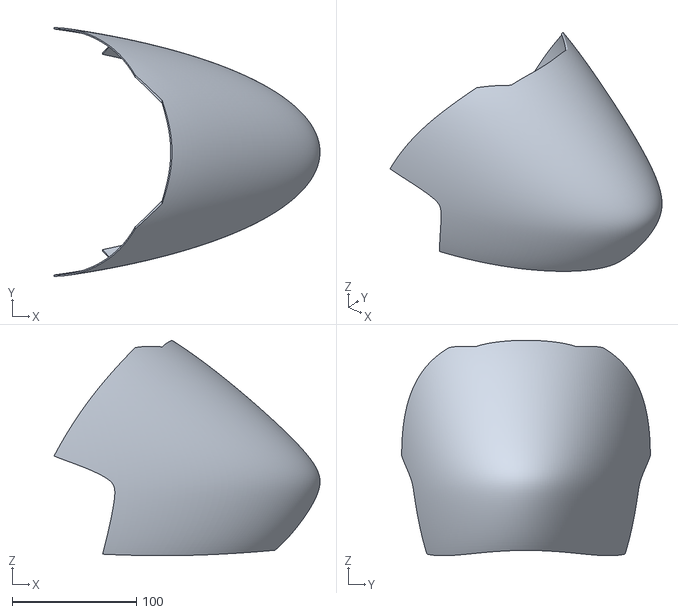
[picture p73: CAD file, 2025-01-01]
EpsilonProtogen/Visor/Visor.stl
214.5 x 200.5 x 173.7
