coelacant1/SigmaProtogen/EpsilonProtogen/VisorBuck.step

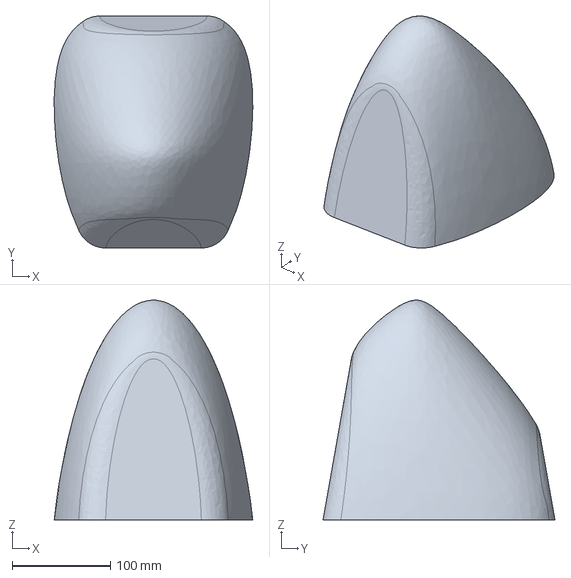
[picture p74: CAD file, 2025-01-01]
EpsilonProtogen/VisorBuck.step
202.5 x 236.5 x 224.1 mm
