coelacant1/SigmaProtogen/Frame/Forehead.stl

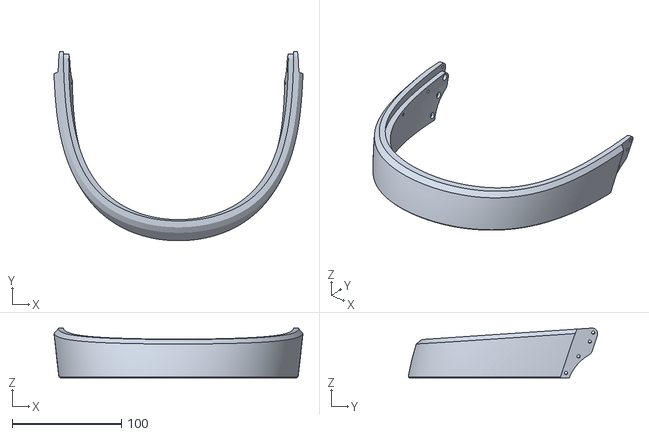
[picture p75: CAD file, 2024-05-18]
Frame/Forehead.stl
227.8 x 173.3 x 45.6
