coelacant1/SigmaProtogen/SigmaProtogen/Displays/InnerCircle.stl

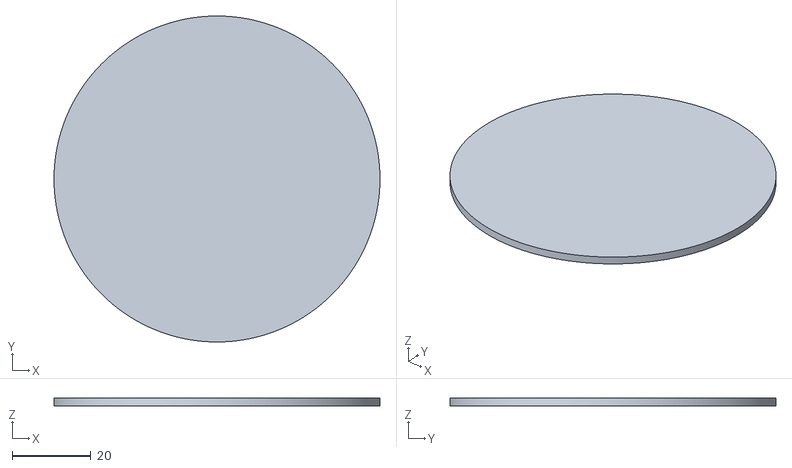
[picture p76: CAD file, 2024-05-18]
SigmaProtogen/Displays/InnerCircle.stl
83.0 x 83.0 x 2.00
