coelacant1/SigmaProtogen/SigmaProtogen/Frame/LongFins/FinRight.stl

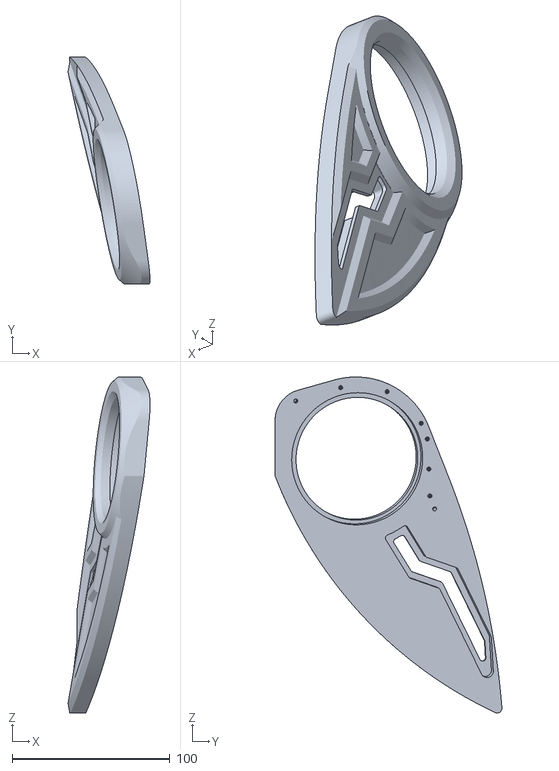
[picture p77: CAD file, 2024-06-20]
SigmaProtogen/Frame/LongFins/FinRight.stl
51.9 x 143.6 x 212.7
