coelacant1/SigmaProtogen/SigmaProtogen/Frame/ShortFins/FinRight.stl

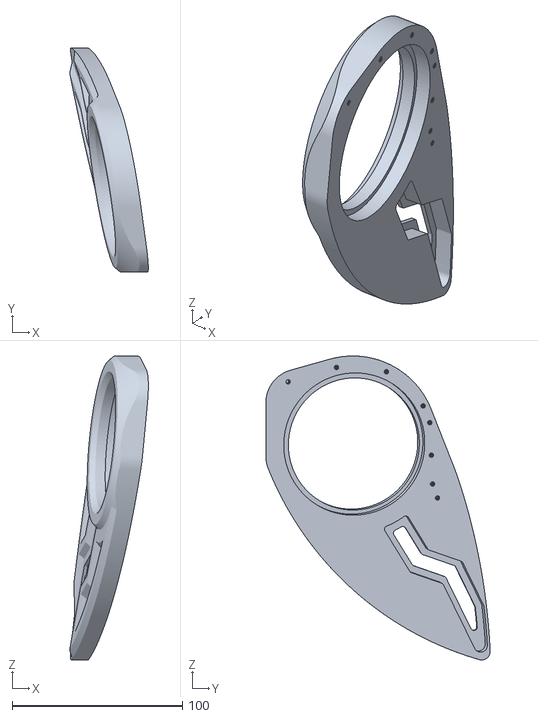
[picture p78: CAD file, 2024-05-21]
SigmaProtogen/Frame/ShortFins/FinRight.stl
46.3 x 131.9 x 178.8
