coelacant1/SigmaProtogen/SigmaProtogen/HUB75/HUB75L_InfillMod.stl

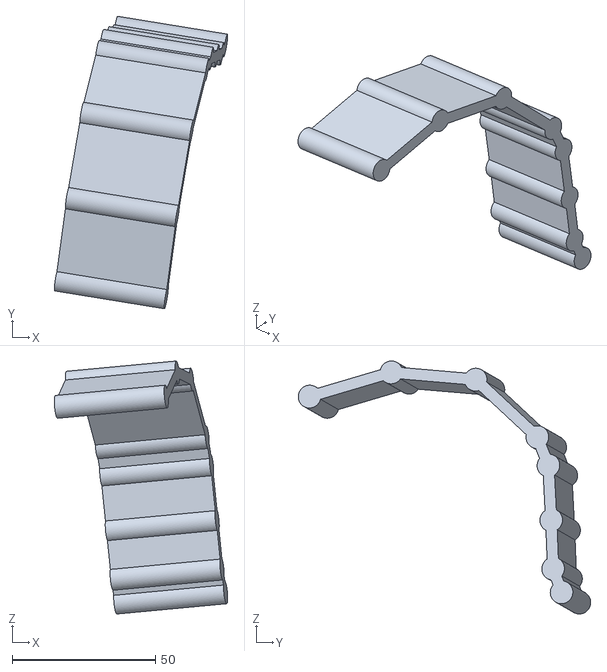
[picture p79: CAD file, 2024-05-19]
SigmaProtogen/HUB75/HUB75L_InfillMod.stl
60.5 x 102.1 x 88.3
