coelacant1/SigmaProtogen/SigmaProtogen/Visor/Mount/ForeheadTopRight.stl

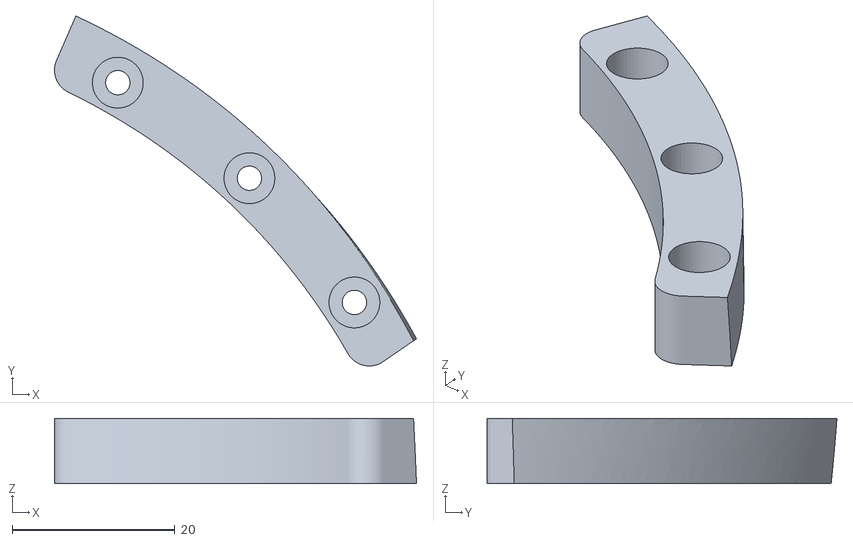
[picture p80: CAD file, 2024-05-18]
SigmaProtogen/Visor/Mount/ForeheadTopRight.stl
44.5 x 43.0 x 8.00
