coelacant1/SigmaProtogen/SigmaProtogen/Visor/Visor.stl

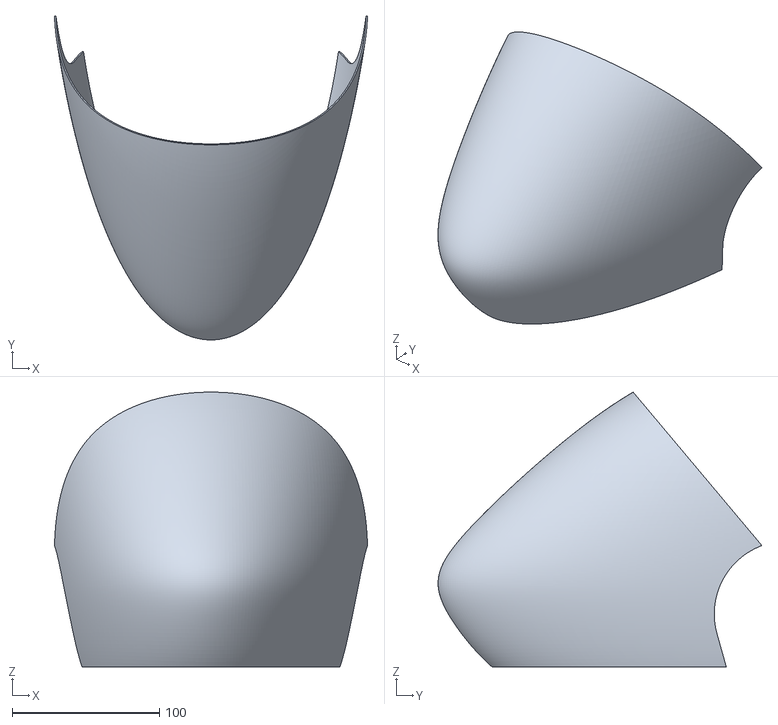
[picture p81: CAD file, 2024-05-18]
SigmaProtogen/Visor/Visor.stl
212.6 x 219.9 x 186.6
