coelacant1/SigmaProtogen/SigmaProtogen/WS35 Rear Panel Frame/RearHelmet_InfillMod.stl

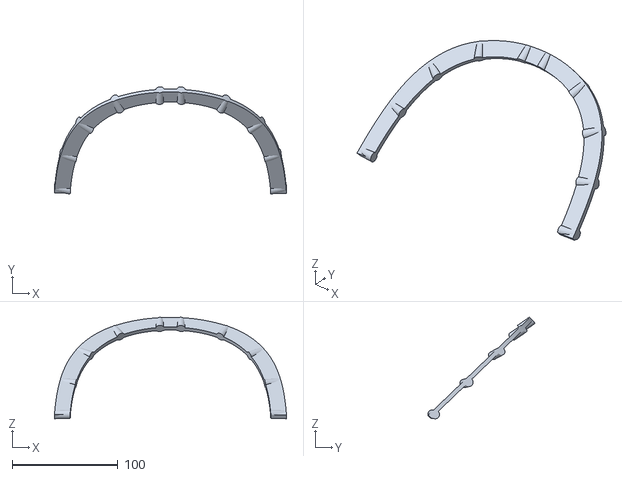
[picture p82: CAD file, 2024-06-12]
SigmaProtogen/WS35 Rear Panel Frame/RearHelmet_InfillMod.stl
219.2 x 101.4 x 96.0
