coelacant1/SigmaProtogen/SigmaProtogen_BambuLabs.3mf

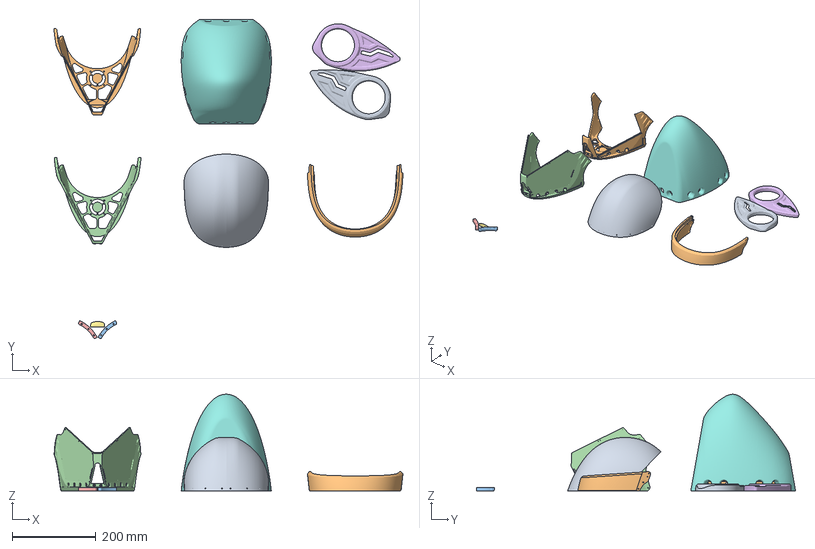
[picture p83: CAD file, 2024-05-18]
SigmaProtogen_BambuLabs.3mf
831.6 x 760.6 x 230.1 mm
RearHelmet.stl
Forehead.stl
ForeheadTopLeft.stl
WS35Face.stl
ForeheadTopRight.stl
FinLeft.stl
MagMntChin.stl
Buck.stl
FinRight.stl
HUB75Face.stl
