coelacant1/SigmaProtogen/WS35/WS35Face.stl

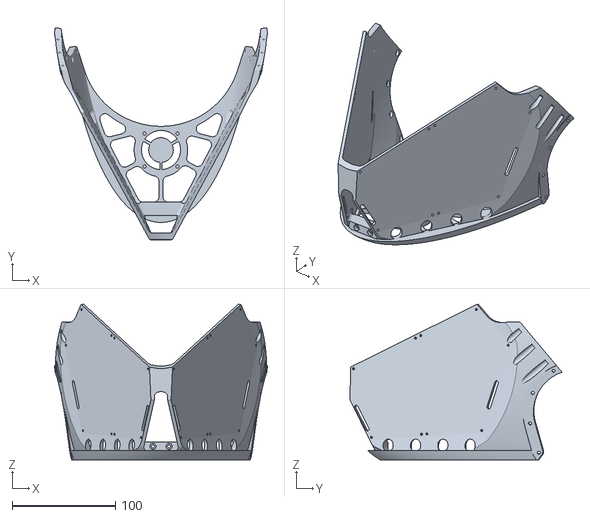
[picture p84: CAD file, 2024-05-18]
WS35/WS35Face.stl
206.6 x 205.8 x 150.9
