coelacant1/SigmaProtogen/BetaProtogen/Frame/FrameForeheadL_V1-1.stl

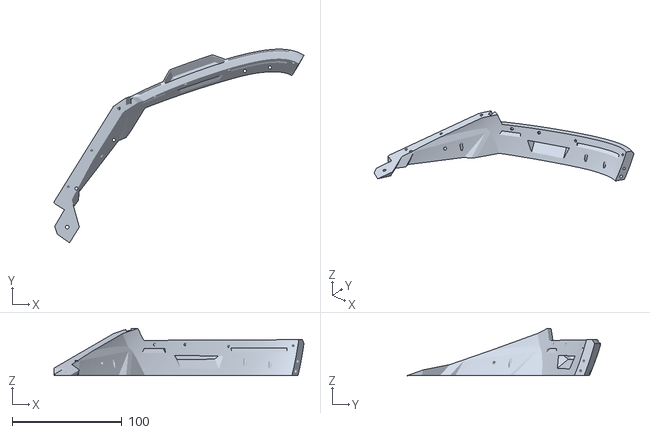
[picture p85: CAD file, 2025-01-01]
BetaProtogen/Frame/FrameForeheadL_V1-1.stl
228.0 x 176.6 x 43.2
