coelacant1/SigmaProtogen/BetaProtogen/LED Cover/LEDBoardCoverRight_V1-0.stl

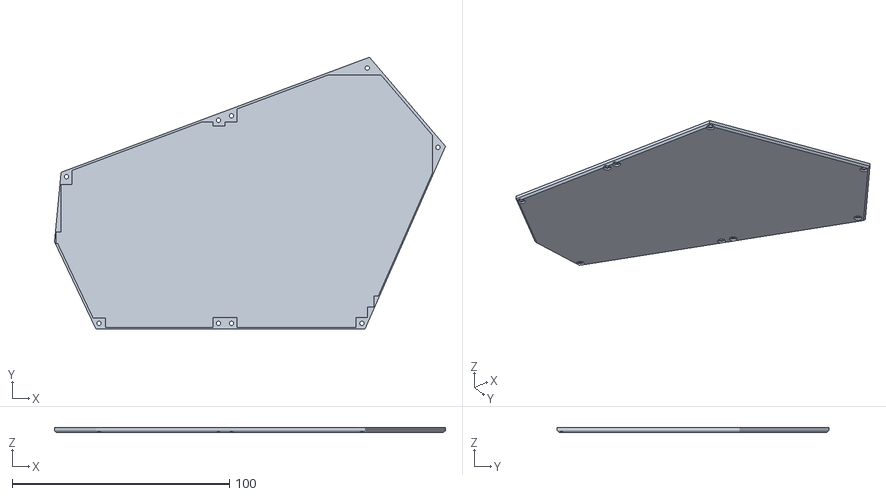
[picture p86: CAD file, 2025-01-01]
BetaProtogen/LED Cover/LEDBoardCoverRight_V1-0.stl
180.0 x 125.0 x 2.50
