coelacant1/SigmaProtogen/BetaProtogen/LED Mount MAX7219/MAX7219LEDEarMountLeft_V1-0.stl

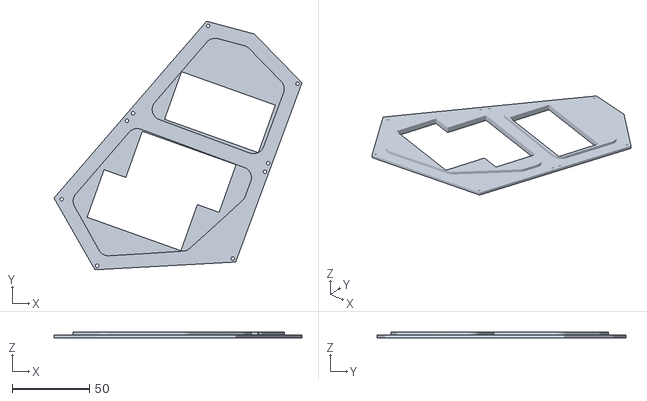
[picture p87: CAD file, 2025-01-01]
BetaProtogen/LED Mount MAX7219/MAX7219LEDEarMountLeft_V1-0.stl
161.0 x 161.3 x 4.00
