coelacant1/SigmaProtogen/BetaProtogen/LED Mount WS35/WS35BendMount_V1-0.stl

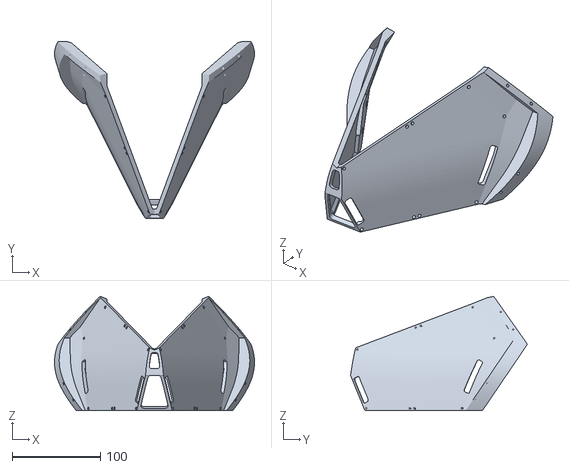
[picture p88: CAD file, 2025-01-01]
BetaProtogen/LED Mount WS35/WS35BendMount_V1-0.stl
226.4 x 200.2 x 129.4
