coelacant1/SigmaProtogen/BetaProtogen/Visor/BuckTopLeft_V3-0.stl

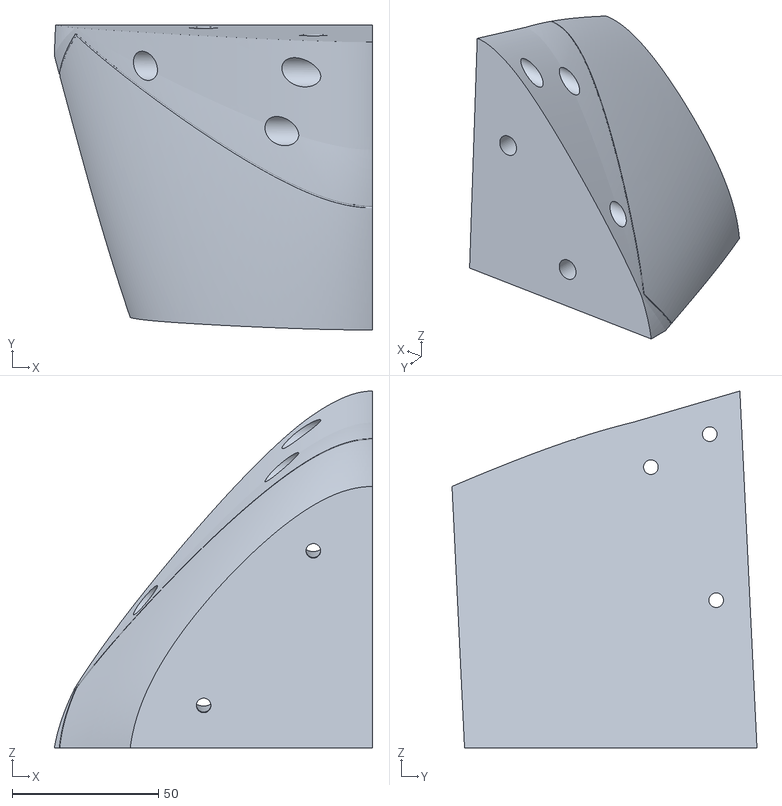
[picture p89: CAD file, 2025-01-01]
BetaProtogen/Visor/BuckTopLeft_V3-0.stl
109.0 x 104.4 x 122.2
