coelacant1/SigmaProtogen/BetaProtogen/VisorMount/BotBackMagnet.stl

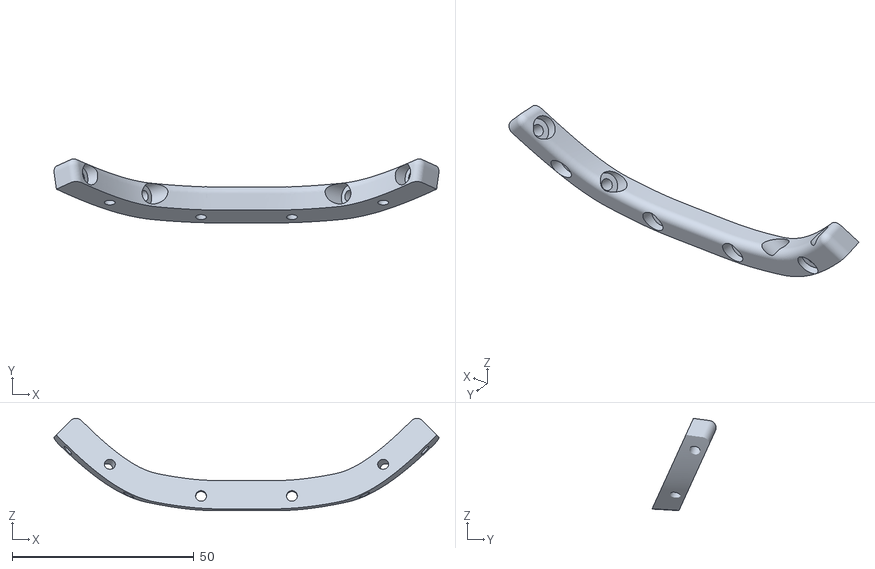
[picture p90: CAD file, 2025-01-01]
BetaProtogen/VisorMount/BotBackMagnet.stl
106.0 x 17.7 x 25.4
