coelacant1/SigmaProtogen/DeltaProtogen/Frame/TopLeftForehead_V1-0.stl

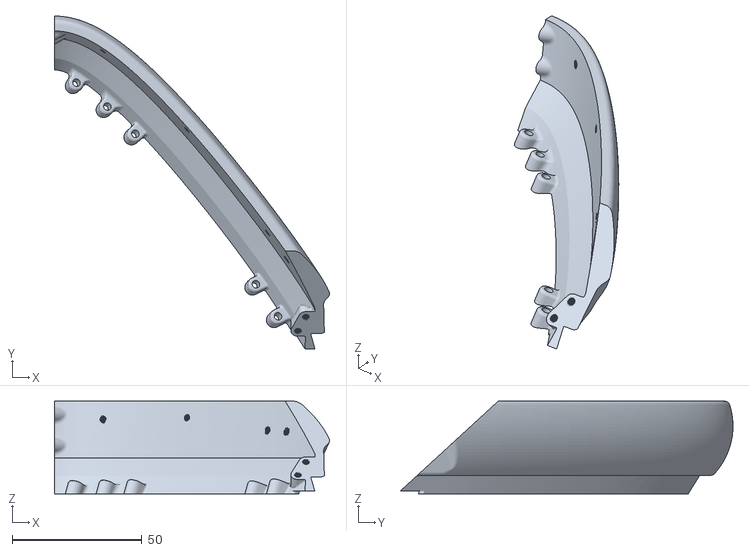
[picture p91: CAD file, 2025-01-01]
DeltaProtogen/Frame/TopLeftForehead_V1-0.stl
106.0 x 128.2 x 35.7
