coelacant1/SigmaProtogen/DeltaProtogen/Hinge/BackHinge_V1-0.stl

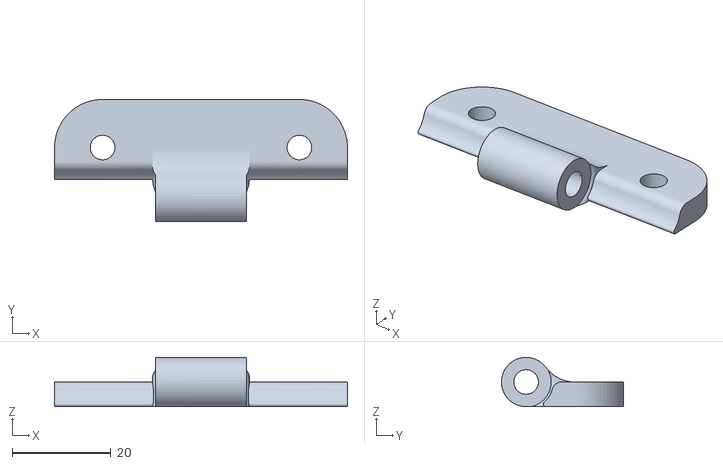
[picture p92: CAD file, 2025-01-01]
DeltaProtogen/Hinge/BackHinge_V1-0.stl
59.4 x 24.8 x 10.00
