coelacant1/SigmaProtogen/DeltaProtogen/LED Mount KS W35/KSWS35_Right_V1-0.stl

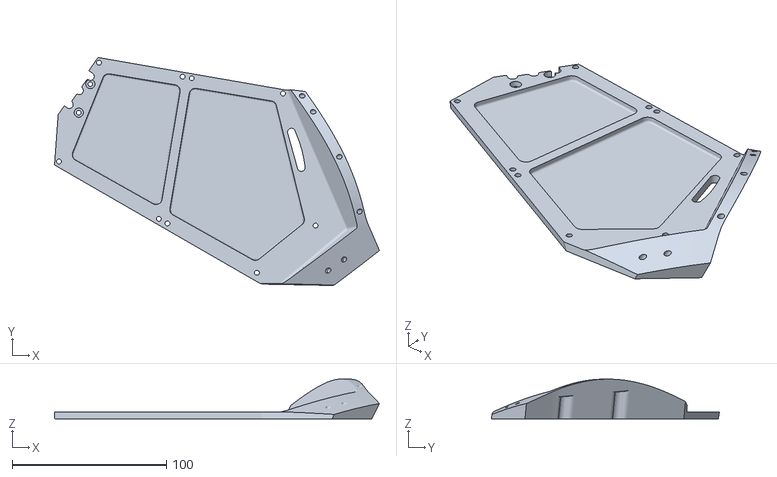
[picture p93: CAD file, 2025-01-01]
DeltaProtogen/LED Mount KS W35/KSWS35_Right_V1-0.stl
210.8 x 147.9 x 25.8
