coelacant1/SigmaProtogen/DeltaProtogen/LED Mount MAX7219/MAX7219BotLeft_V1-0.stl

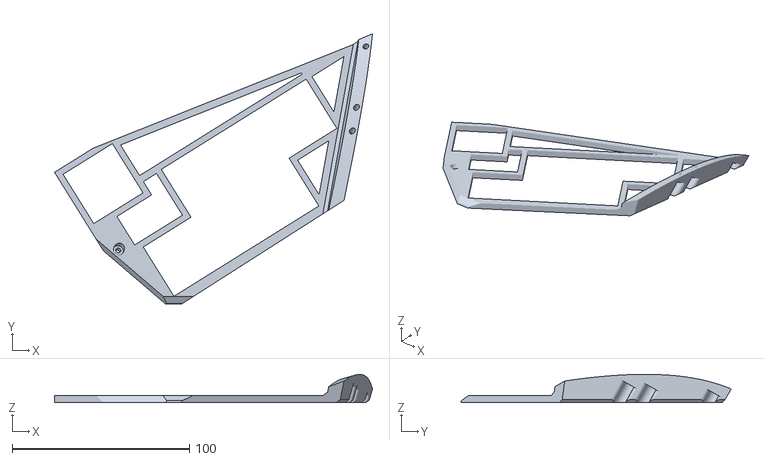
[picture p94: CAD file, 2025-01-01]
DeltaProtogen/LED Mount MAX7219/MAX7219BotLeft_V1-0.stl
179.5 x 152.7 x 16.0
