coelacant1/SigmaProtogen/DeltaProtogen/LED Mount P3 HUB75/P3Nose_V1-0.stl

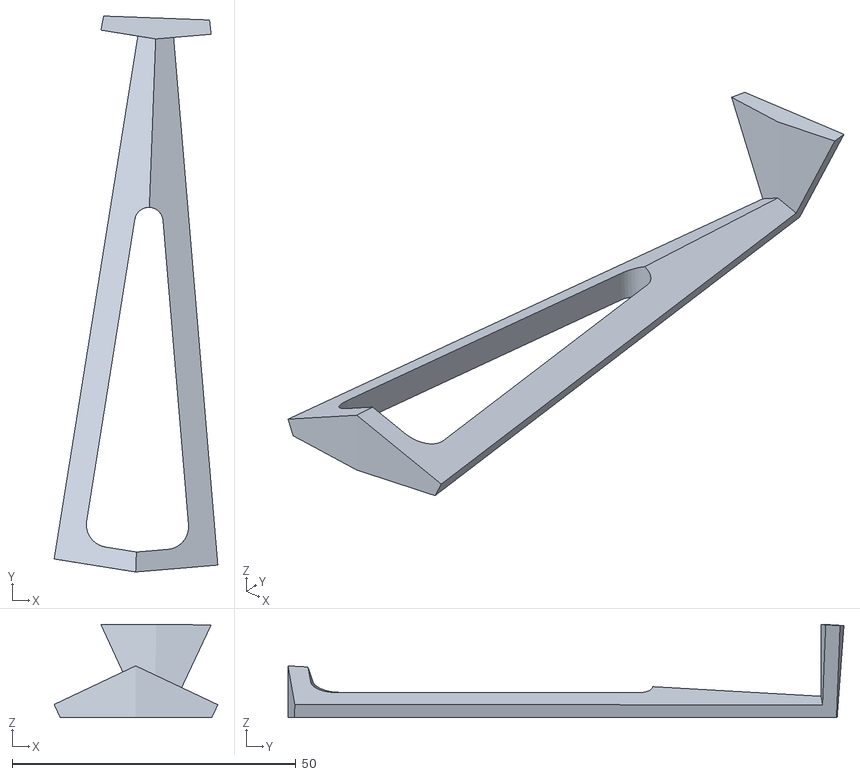
[picture p95: CAD file, 2025-01-01]
DeltaProtogen/LED Mount P3 HUB75/P3Nose_V1-0.stl
28.9 x 98.0 x 16.4
