coelacant1/SigmaProtogen/DeltaProtogen/Side Displays/RightPuck_V1-0.stl

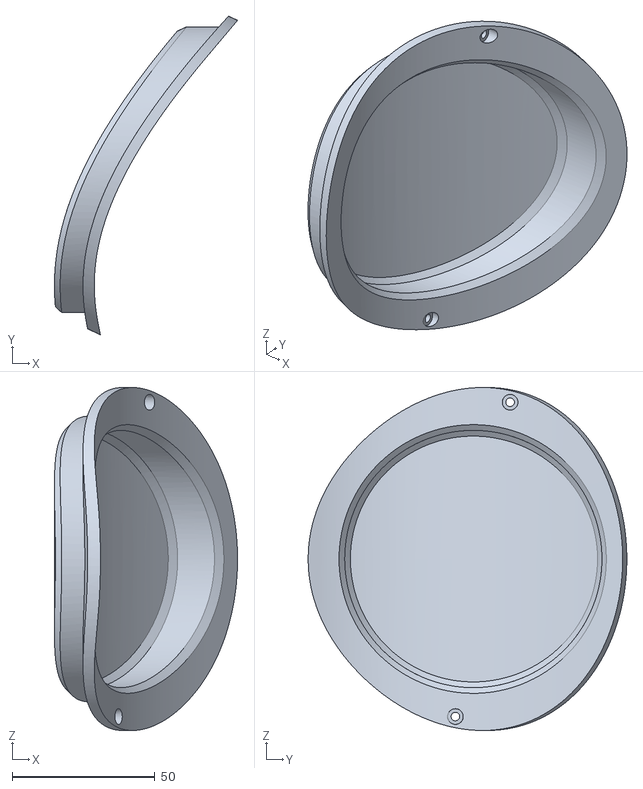
[picture p96: CAD file, 2025-01-01]
DeltaProtogen/Side Displays/RightPuck_V1-0.stl
64.1 x 111.5 x 120.0
