coelacant1/SigmaProtogen/DeltaProtogen/Visor Mounts/VisorSupportTopCover.stl

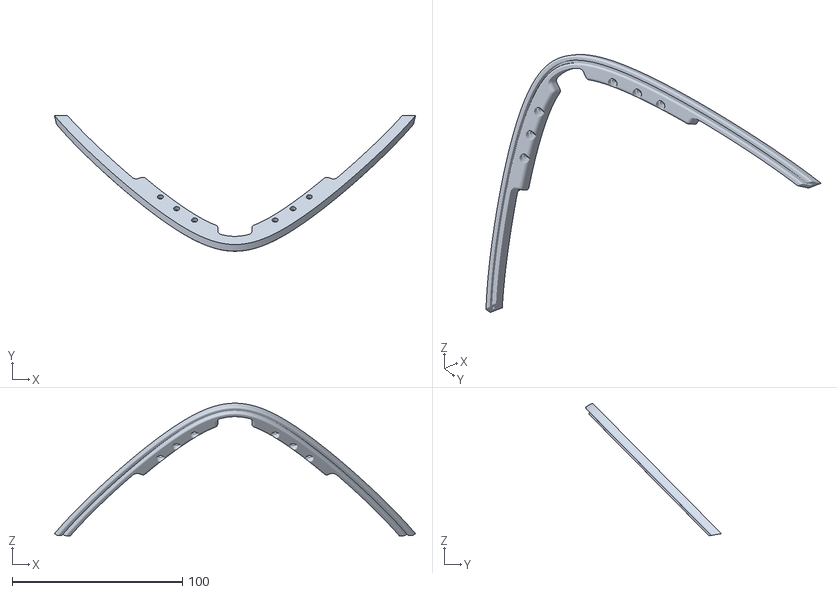
[picture p97: CAD file, 2025-01-01]
DeltaProtogen/Visor Mounts/VisorSupportTopCover.stl
212.1 x 79.6 x 77.9
