coelacant1/SigmaProtogen/DeltaProtogen/Visor/VisorCoverTop_V1-0.stl

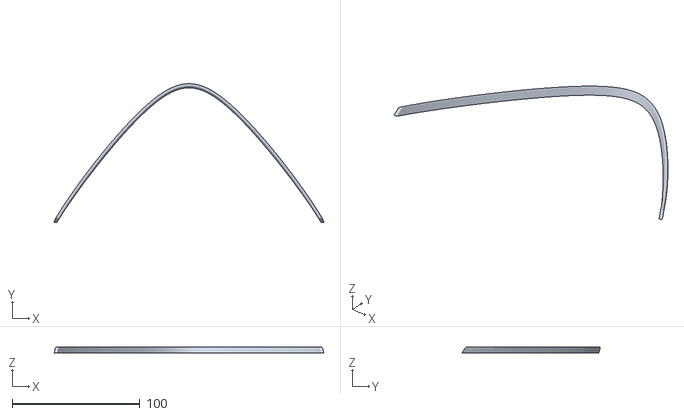
[picture p98: CAD file, 2025-01-01]
DeltaProtogen/Visor/VisorCoverTop_V1-0.stl
211.7 x 108.7 x 5.00
