coelacant1/SigmaProtogen/EpsilonProtogen/Frame Connectors/FrontHelmetJoin.stl

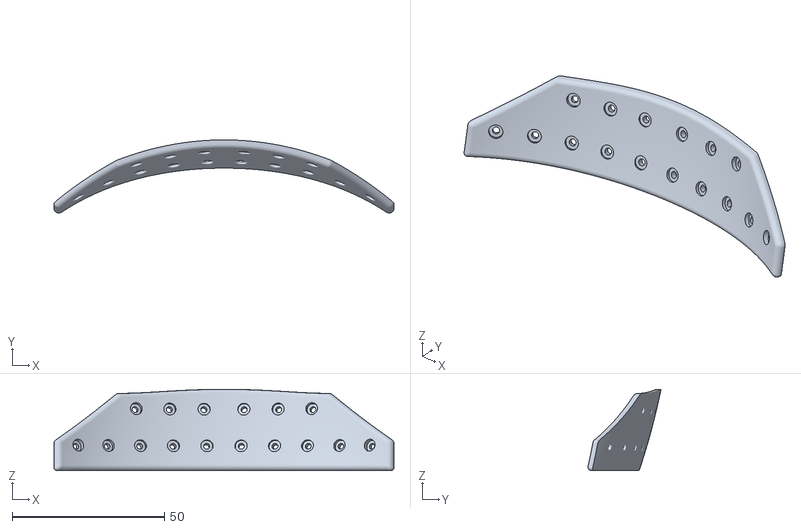
[picture p99: CAD file, 2025-01-01]
EpsilonProtogen/Frame Connectors/FrontHelmetJoin.stl
111.7 x 24.0 x 26.8
