coelacant1/SigmaProtogen/EpsilonProtogen/Frame/Left/RearFinLeft.stl

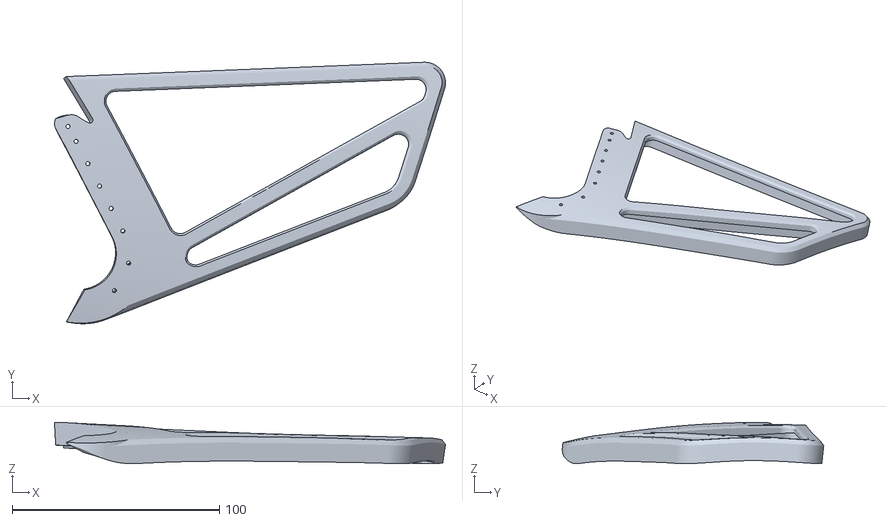
[picture p100: CAD file, 2025-01-01]
EpsilonProtogen/Frame/Left/RearFinLeft.stl
188.8 x 126.3 x 20.0
