coelacant1/SigmaProtogen/EpsilonProtogen/Frame/Right/RearTopFinDisplay.stl

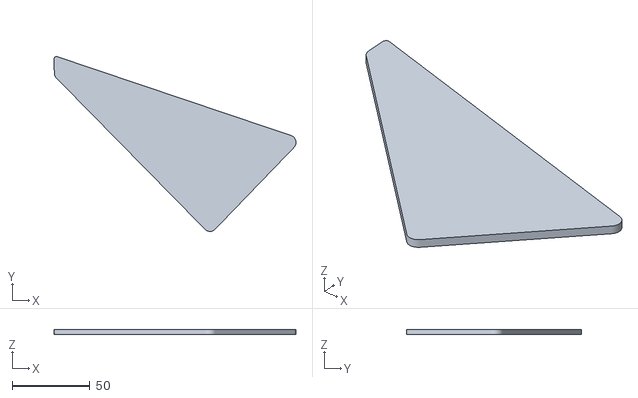
[picture p101: CAD file, 2025-01-01]
EpsilonProtogen/Frame/Right/RearTopFinDisplay.stl
155.2 x 112.3 x 3.29
