coelacant1/SigmaProtogen/EpsilonProtogen/HUB75/HUB75Face.stl

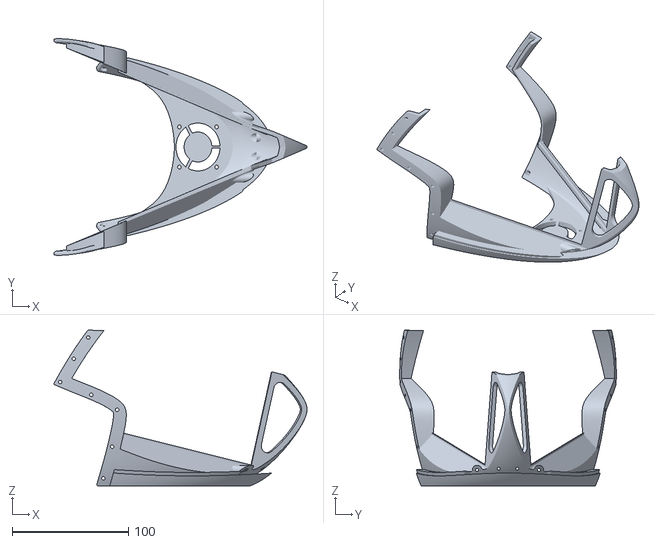
[picture p102: CAD file, 2025-01-01]
EpsilonProtogen/HUB75/HUB75Face.stl
217.9 x 186.5 x 134.1
