coelacant1/SigmaProtogen/EpsilonProtogen/Visor/Buck.stl

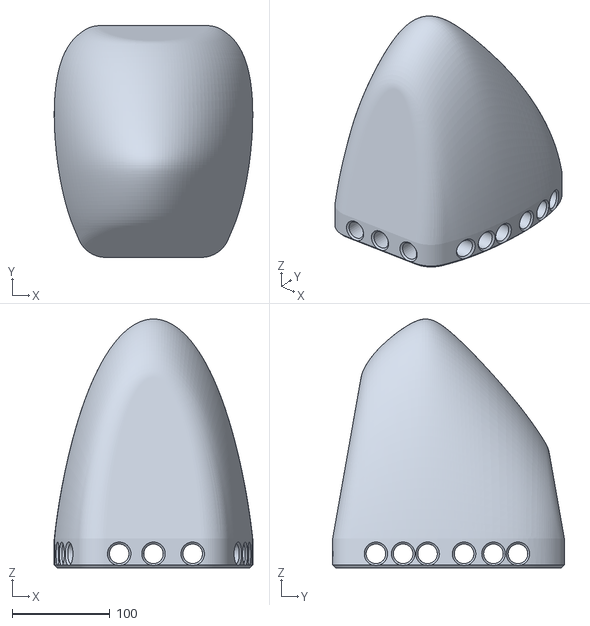
[picture p103: CAD file, 2025-01-01]
EpsilonProtogen/Visor/Buck.stl
202.6 x 236.5 x 254.1
