coelacant1/SigmaProtogen/SigmaProtogen/Displays/RearLEDCoverLeft.stl

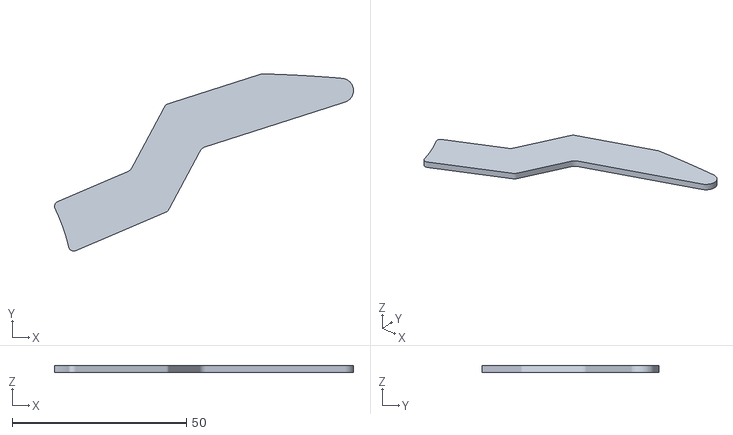
[picture p104: CAD file, 2024-05-18]
SigmaProtogen/Displays/RearLEDCoverLeft.stl
85.8 x 50.8 x 2.00
