coelacant1/SigmaProtogen/SigmaProtogen/Visor/Mount/MagMntChin.stl

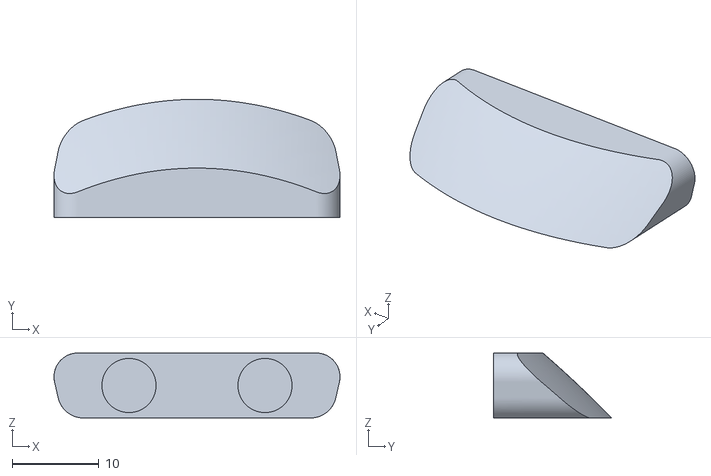
[picture p105: CAD file, 2024-05-18]
SigmaProtogen/Visor/Mount/MagMntChin.stl
33.0 x 13.7 x 7.50
