coelacant1/SigmaProtogen/SigmaProtogen/WS35 Rear Panel Frame/Forehead_InfillMod.stl

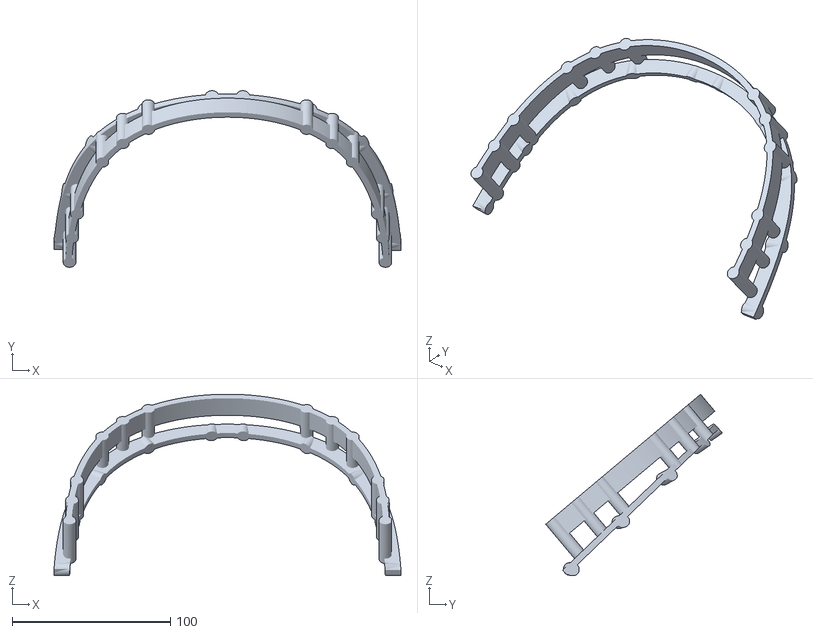
[picture p106: CAD file, 2024-06-12]
SigmaProtogen/WS35 Rear Panel Frame/Forehead_InfillMod.stl
219.2 x 111.6 x 114.7
