coelacant1/SigmaProtogen/BetaProtogen/Frame/FrameChinR_V1-1.stl

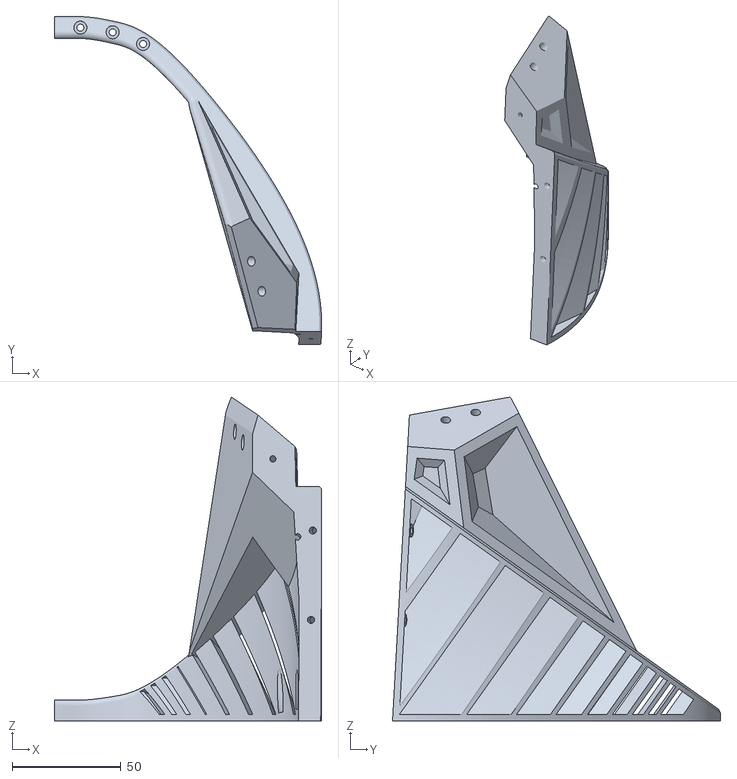
[picture p107: CAD file, 2025-01-01]
BetaProtogen/Frame/FrameChinR_V1-1.stl
123.0 x 150.9 x 149.0
