coelacant1/SigmaProtogen/BetaProtogen/Latch/LatchLeftMount_V1-0.stl

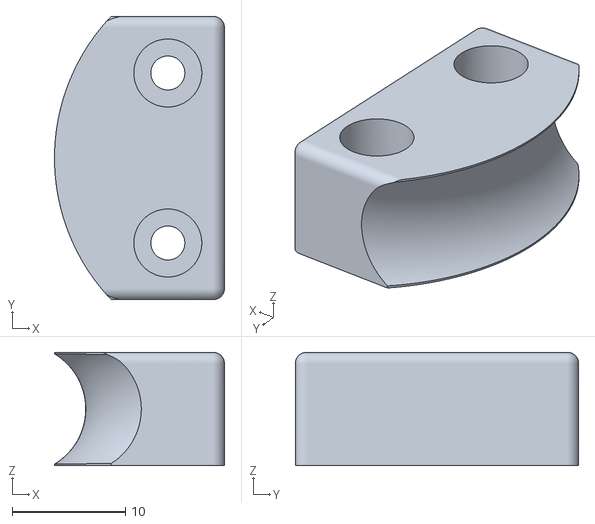
[picture p108: CAD file, 2025-01-01]
BetaProtogen/Latch/LatchLeftMount_V1-0.stl
15.0 x 25.0 x 10.0
