coelacant1/SigmaProtogen/BetaProtogen/LED Mount MAX7219/MAX7219LEDEarMountRight_V1-0.stl

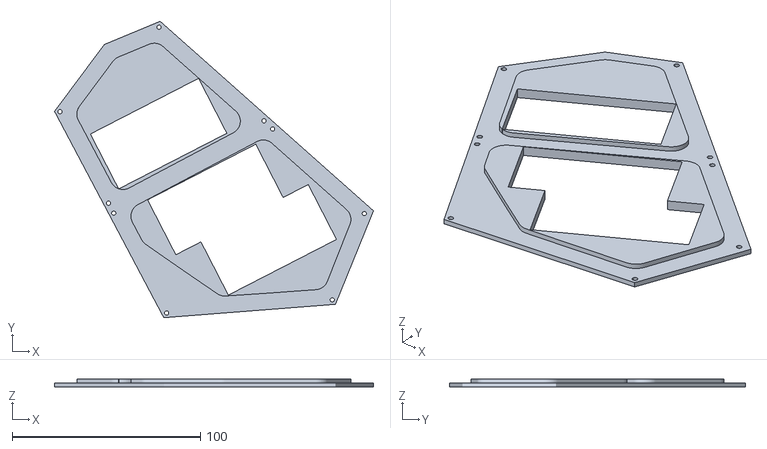
[picture p109: CAD file, 2025-01-01]
BetaProtogen/LED Mount MAX7219/MAX7219LEDEarMountRight_V1-0.stl
169.4 x 157.4 x 4.00
