coelacant1/SigmaProtogen/BetaProtogen/LED Mount WS35/WS35FlatMountConnector_V1-0.stl

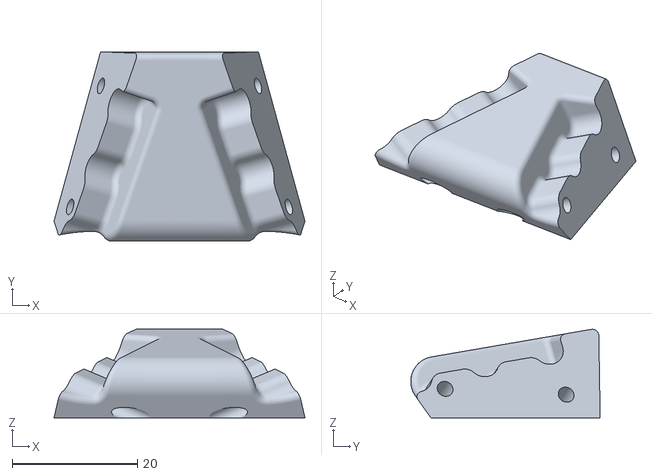
[picture p110: CAD file, 2025-01-01]
BetaProtogen/LED Mount WS35/WS35FlatMountConnector_V1-0.stl
40.2 x 30.3 x 14.2
