coelacant1/SigmaProtogen/BetaProtogen/VisorMount/TopBackMagnet.stl

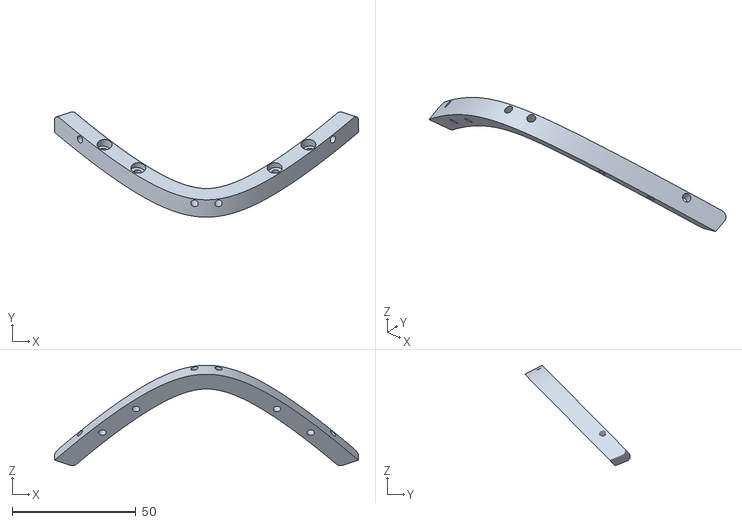
[picture p111: CAD file, 2025-01-01]
BetaProtogen/VisorMount/TopBackMagnet.stl
122.6 x 42.5 x 40.5
