coelacant1/SigmaProtogen/DeltaProtogen/Frame/RightHead_V1-0.stl

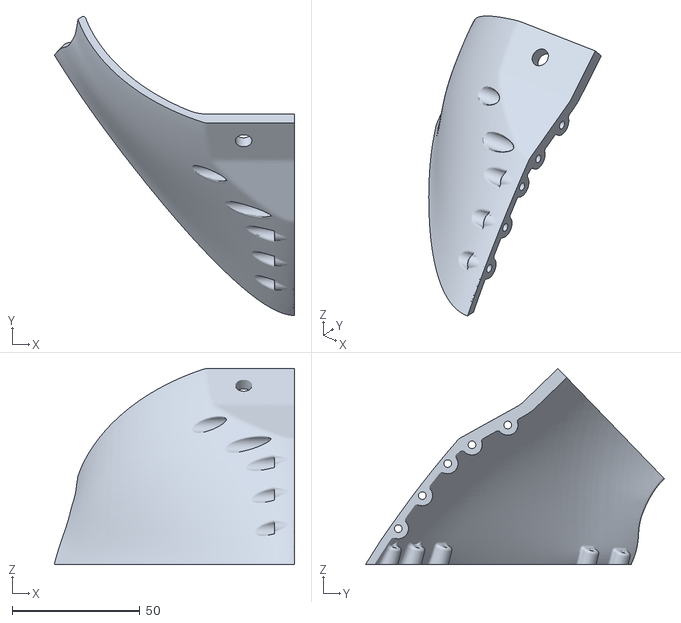
[picture p112: CAD file, 2025-01-01]
DeltaProtogen/Frame/RightHead_V1-0.stl
94.1 x 117.0 x 76.7
