coelacant1/SigmaProtogen/DeltaProtogen/LED Mount MAX7219/MAX7219TopRight_V1-0.stl

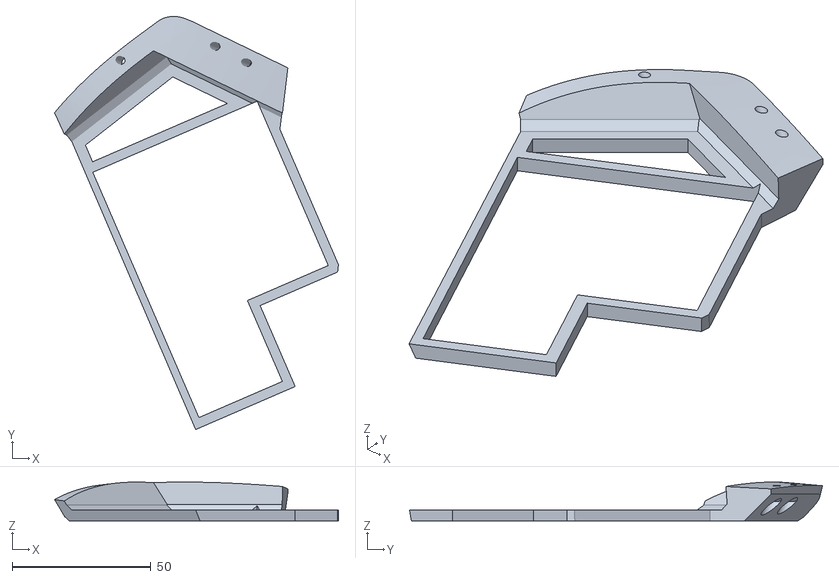
[picture p113: CAD file, 2025-01-01]
DeltaProtogen/LED Mount MAX7219/MAX7219TopRight_V1-0.stl
102.4 x 149.0 x 14.0
