coelacant1/SigmaProtogen/DeltaProtogen/LED Mount P3 HUB75/P3RightMount_V1-0.stl

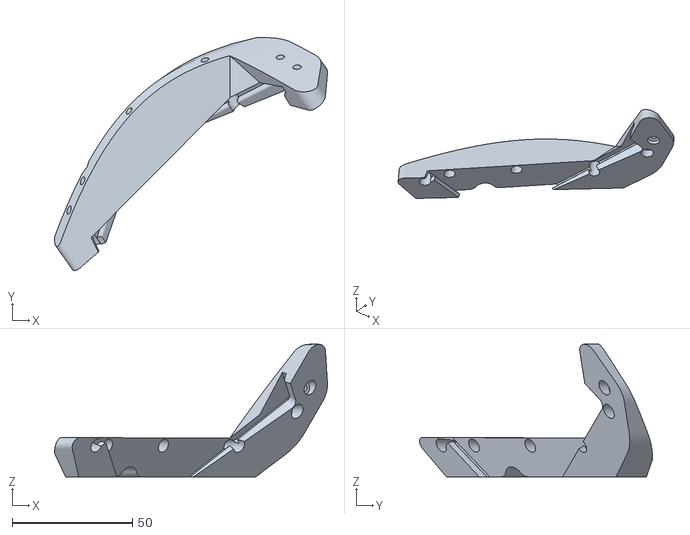
[picture p114: CAD file, 2025-01-01]
DeltaProtogen/LED Mount P3 HUB75/P3RightMount_V1-0.stl
113.7 x 97.0 x 55.2
