coelacant1/SigmaProtogen/DeltaProtogen/Visor Mounts/VisorSupportBottomCover.stl

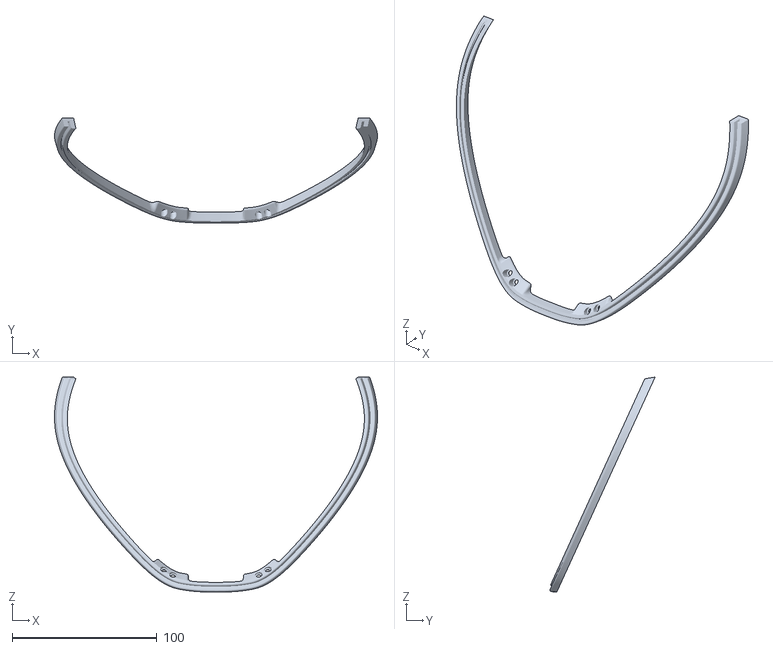
[picture p115: CAD file, 2025-01-01]
DeltaProtogen/Visor Mounts/VisorSupportBottomCover.stl
222.9 x 72.7 x 148.4
