coelacant1/SigmaProtogen/DeltaProtogen/Visor/VisorCoverBottom_V1-0.stl

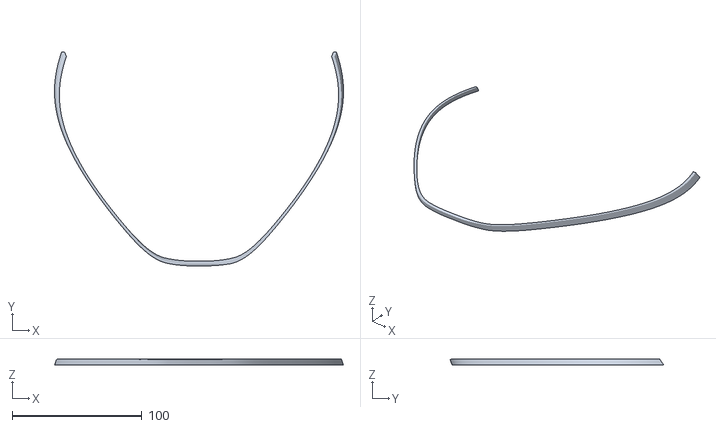
[picture p116: CAD file, 2025-01-01]
DeltaProtogen/Visor/VisorCoverBottom_V1-0.stl
222.6 x 164.7 x 5.00
