coelacant1/SigmaProtogen/EpsilonProtogen/Frame Connectors/HelmetJoin2.stl

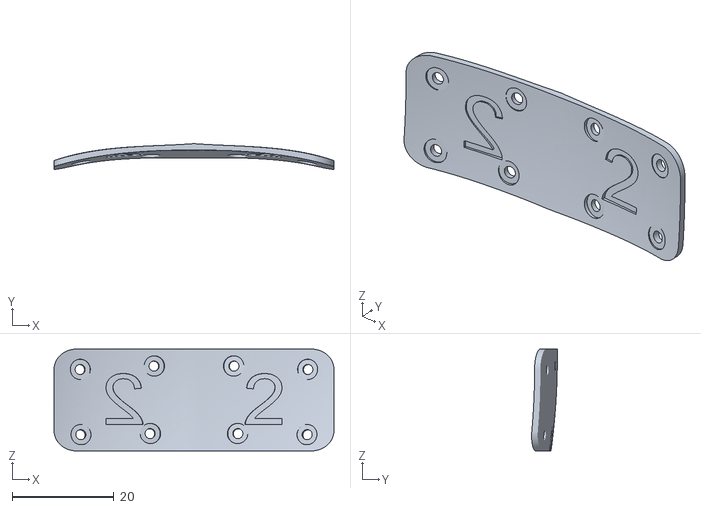
[picture p117: CAD file, 2025-01-01]
EpsilonProtogen/Frame Connectors/HelmetJoin2.stl
55.0 x 5.06 x 20.0
