coelacant1/SigmaProtogen/EpsilonProtogen/Frame/Left/RearBottomFinDisplay.stl

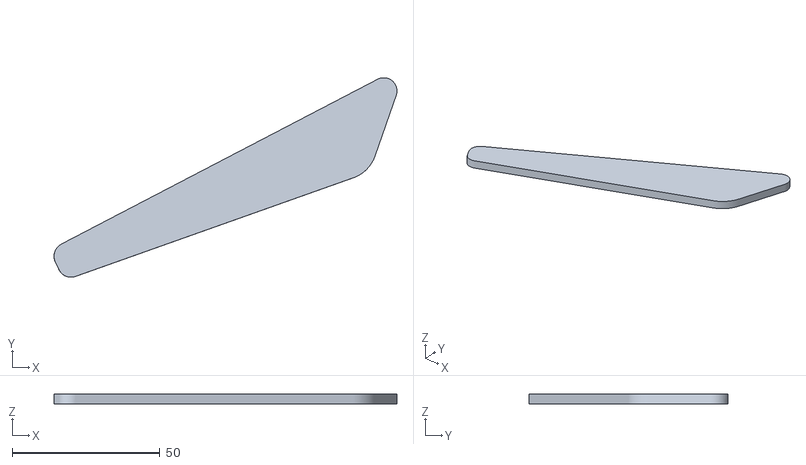
[picture p118: CAD file, 2025-01-01]
EpsilonProtogen/Frame/Left/RearBottomFinDisplay.stl
115.9 x 67.4 x 3.29
