coelacant1/SigmaProtogen/EpsilonProtogen/Visor/Mount/MagMntChin.stl

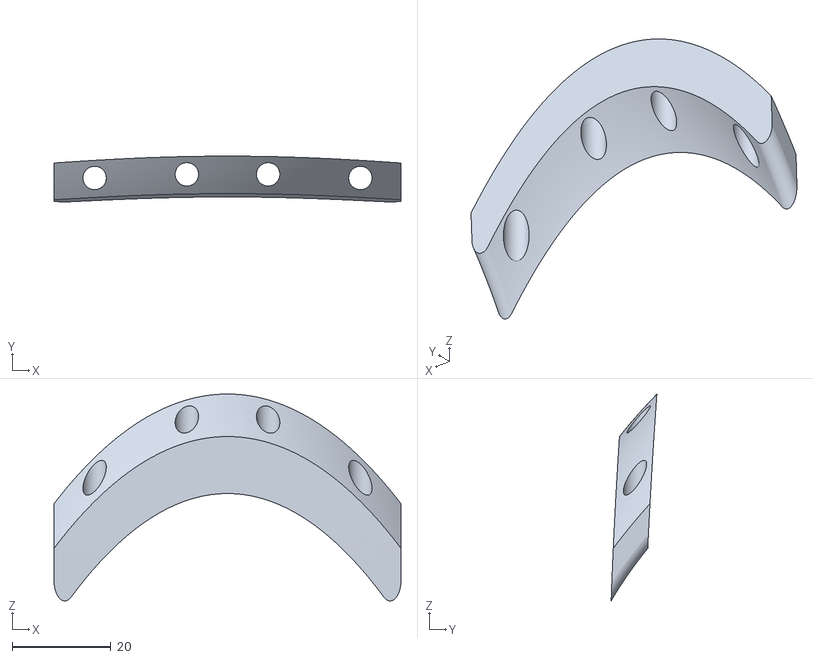
[picture p119: CAD file, 2025-01-01]
EpsilonProtogen/Visor/Mount/MagMntChin.stl
70.5 x 9.29 x 42.0
