coelacant1/SigmaProtogen/SigmaProtogen/Displays/RearLEDCoverRight.stl

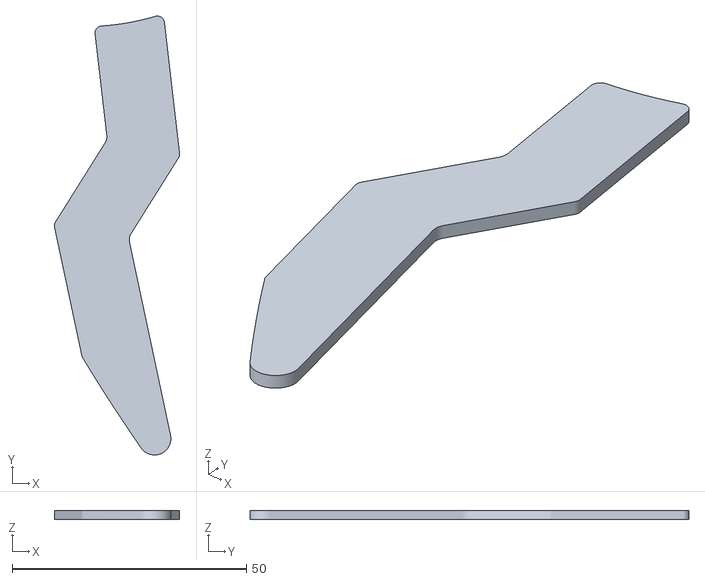
[picture p120: CAD file, 2024-05-18]
SigmaProtogen/Displays/RearLEDCoverRight.stl
26.7 x 93.7 x 2.00
