coelacant1/SigmaProtogen/SigmaProtogen/Frame/LongFins/RearLEDCoverRight.stl

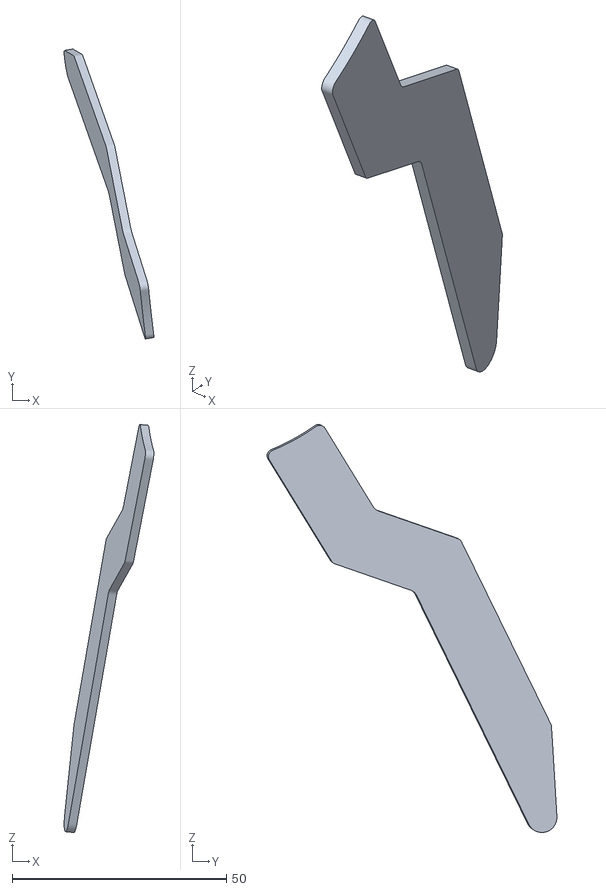
[picture p121: CAD file, 2024-06-20]
SigmaProtogen/Frame/LongFins/RearLEDCoverRight.stl
21.0 x 67.7 x 95.3
