coelacant1/SigmaProtogen/SigmaProtogen/HUB75/HUB75Face.stl

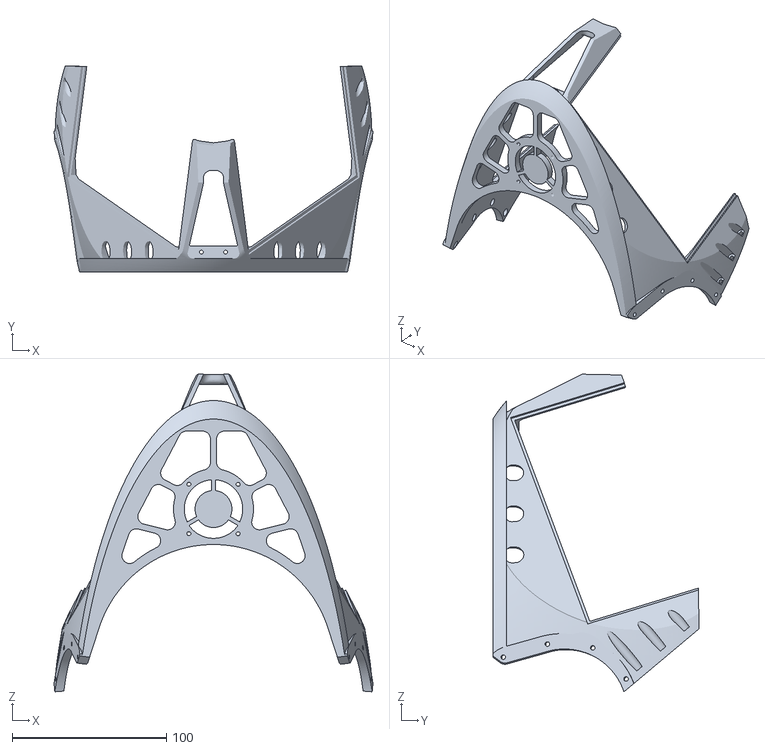
[picture p122: CAD file, 2024-05-19]
SigmaProtogen/HUB75/HUB75Face.stl
206.6 x 133.7 x 205.8
