coelacant1/SigmaProtogen/BetaProtogen/Frame/FrameForeheadR_V1-1.stl

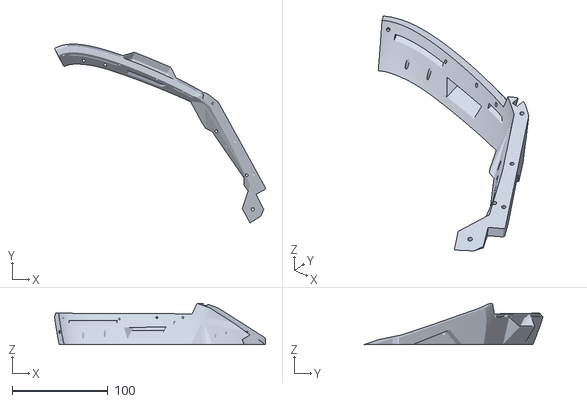
[picture p123: CAD file, 2025-01-01]
BetaProtogen/Frame/FrameForeheadR_V1-1.stl
220.4 x 186.8 x 43.2
