coelacant1/SigmaProtogen/BetaProtogen/Latch/LatchOuterRotate_V1-0.stl

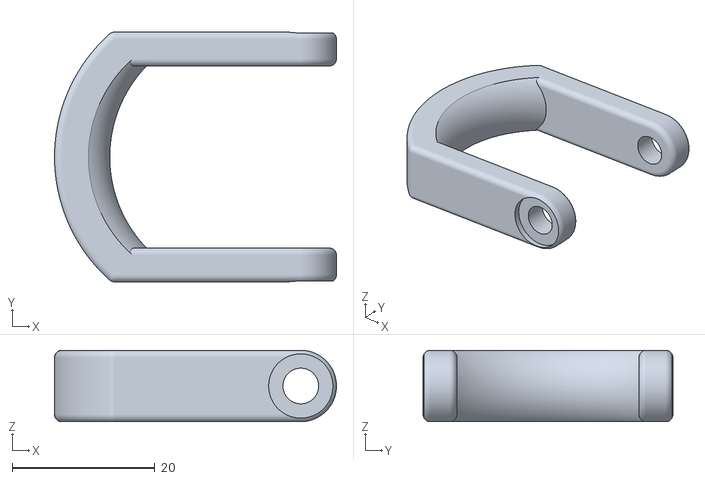
[picture p124: CAD file, 2025-01-01]
BetaProtogen/Latch/LatchOuterRotate_V1-0.stl
39.5 x 35.0 x 10.0
