coelacant1/SigmaProtogen/BetaProtogen/LED Mount MAX7219/MAX7219TopLeft_V1-0.stl

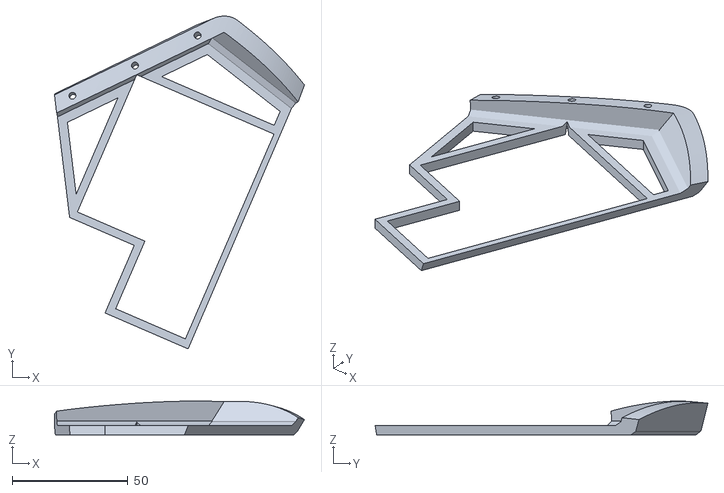
[picture p125: CAD file, 2025-01-01]
BetaProtogen/LED Mount MAX7219/MAX7219TopLeft_V1-0.stl
108.0 x 143.8 x 14.6
