coelacant1/SigmaProtogen/BetaProtogen/VisorMount/TopFrontMagnet.stl

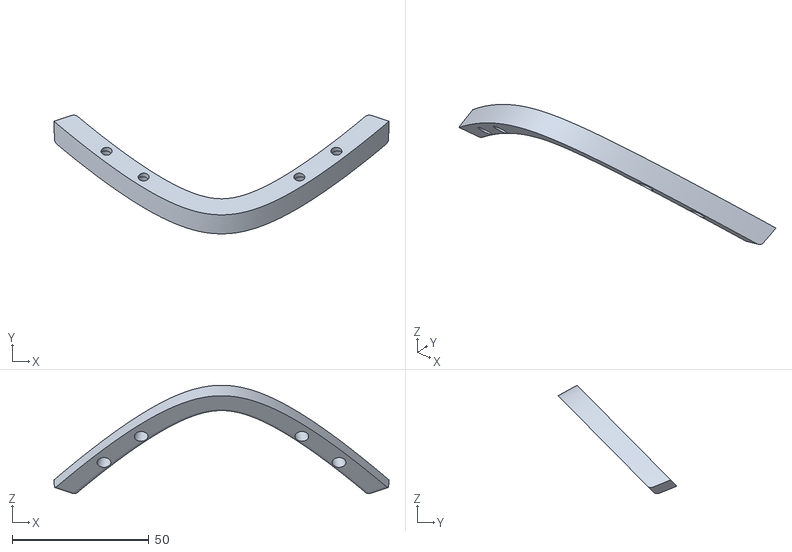
[picture p126: CAD file, 2025-01-01]
BetaProtogen/VisorMount/TopFrontMagnet.stl
122.5 x 43.4 x 39.7
