coelacant1/SigmaProtogen/DeltaProtogen/Frame/LeftJaw_V1-0.stl

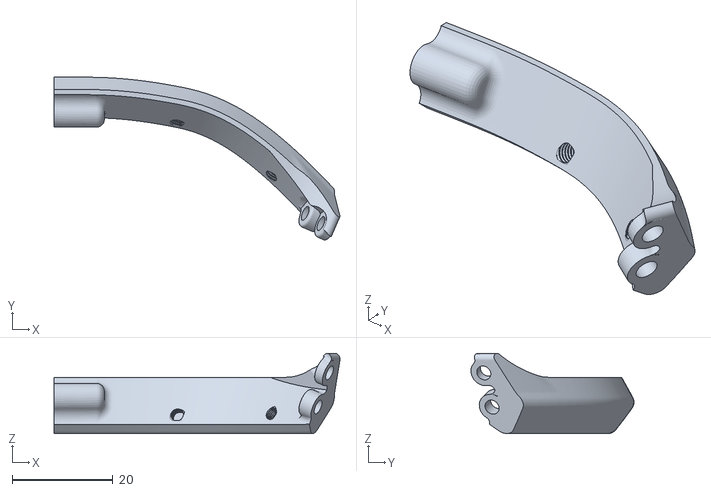
[picture p127: CAD file, 2025-01-01]
DeltaProtogen/Frame/LeftJaw_V1-0.stl
56.7 x 32.4 x 15.9
