coelacant1/SigmaProtogen/DeltaProtogen/Latch/LatchRightMount_V1-0.stl

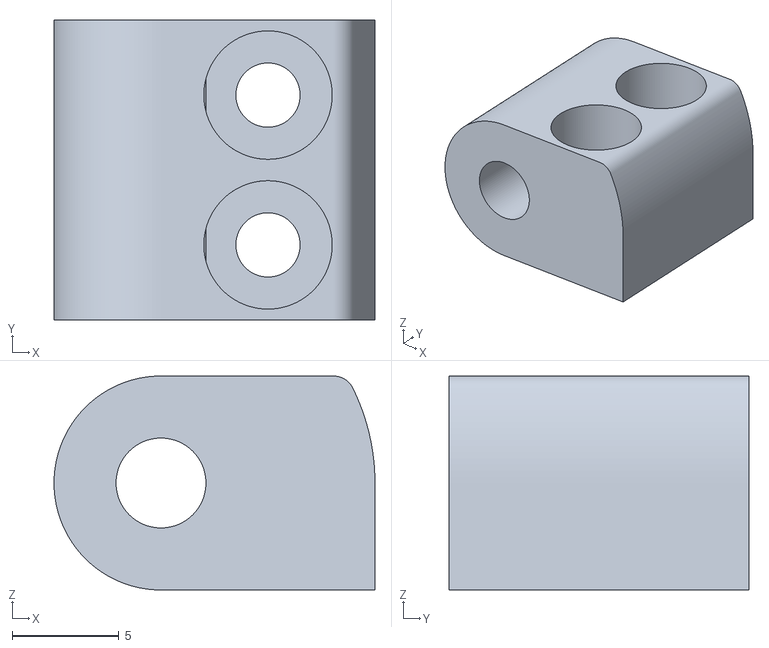
[picture p128: CAD file, 2025-01-01]
DeltaProtogen/Latch/LatchRightMount_V1-0.stl
15.0 x 14.0 x 10.0
