coelacant1/SigmaProtogen/DeltaProtogen/LED Mount MAX7219/MAX7219Connector_V1-0.stl

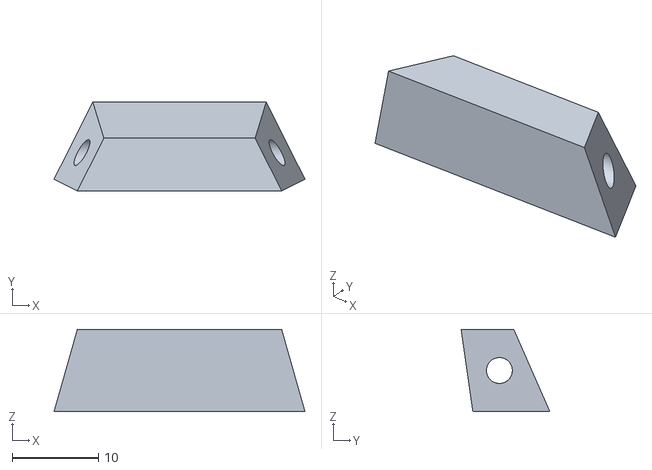
[picture p129: CAD file, 2025-01-01]
DeltaProtogen/LED Mount MAX7219/MAX7219Connector_V1-0.stl
29.1 x 10.3 x 9.53
