coelacant1/SigmaProtogen/DeltaProtogen/Side Displays/RightPuckInner_V1-0.stl

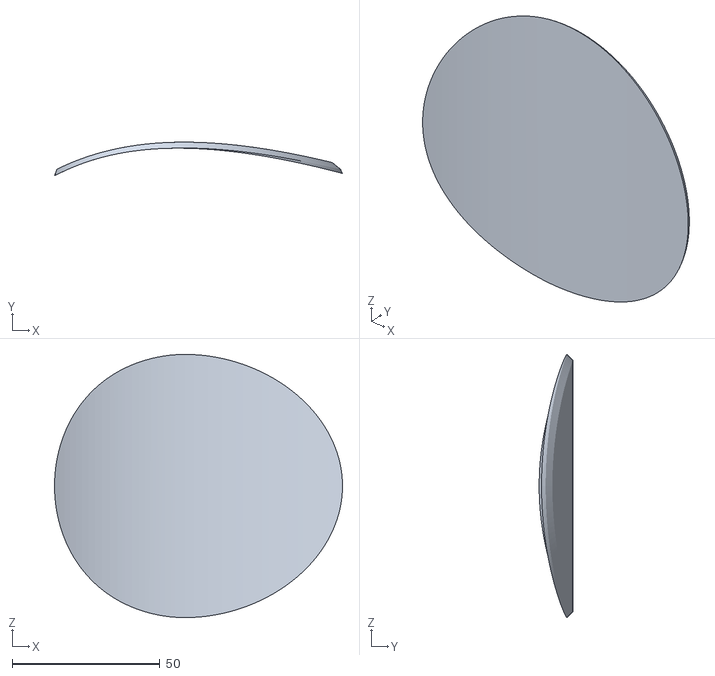
[picture p130: CAD file, 2025-01-01]
DeltaProtogen/Side Displays/RightPuckInner_V1-0.stl
97.4 x 11.4 x 89.0
