coelacant1/SigmaProtogen/DeltaProtogen/Visor Mounts/VisorSupportBottom.stl

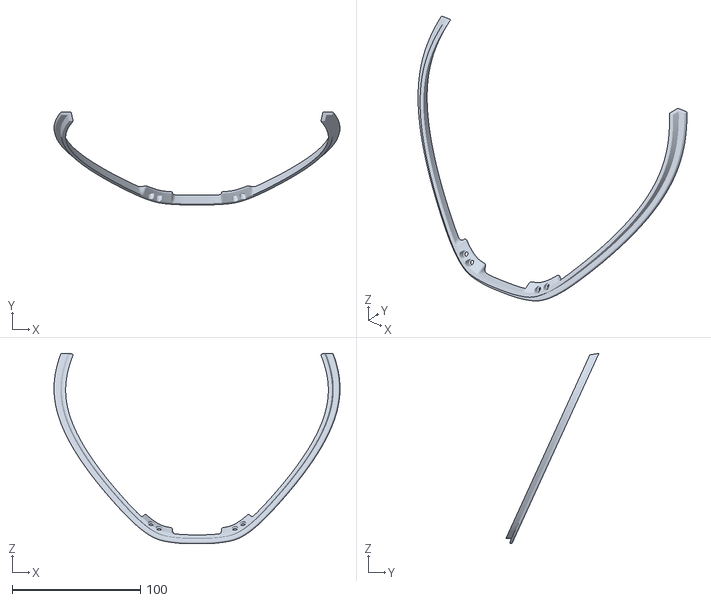
[picture p131: CAD file, 2025-01-01]
DeltaProtogen/Visor Mounts/VisorSupportBottom.stl
223.2 x 72.6 x 148.6
