coelacant1/SigmaProtogen/DeltaProtogen/Visor/Buck_V2-0.stl

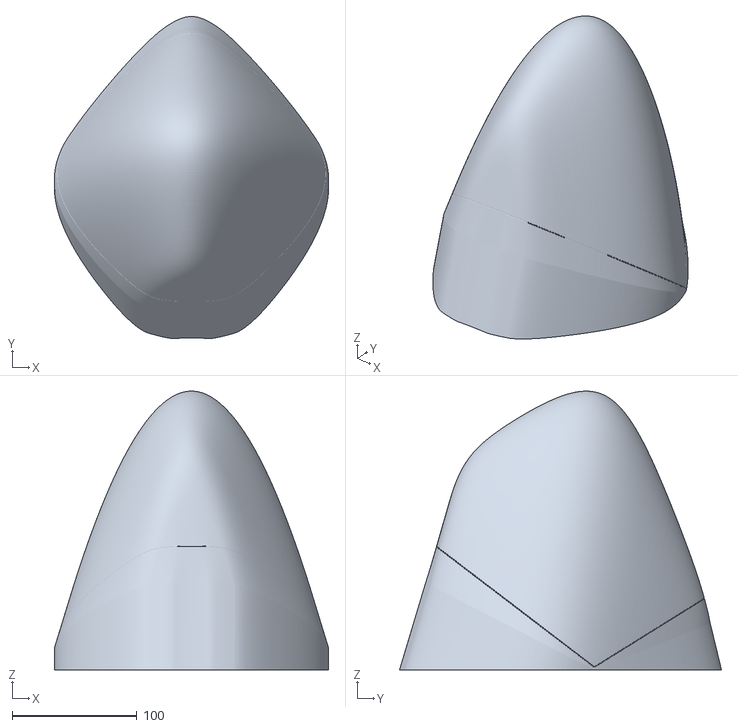
[picture p132: CAD file, 2025-01-01]
DeltaProtogen/Visor/Buck_V2-0.stl
219.7 x 257.7 x 223.1
