coelacant1/SigmaProtogen/EpsilonProtogen/Frame Connectors/HelmetJoin1.stl

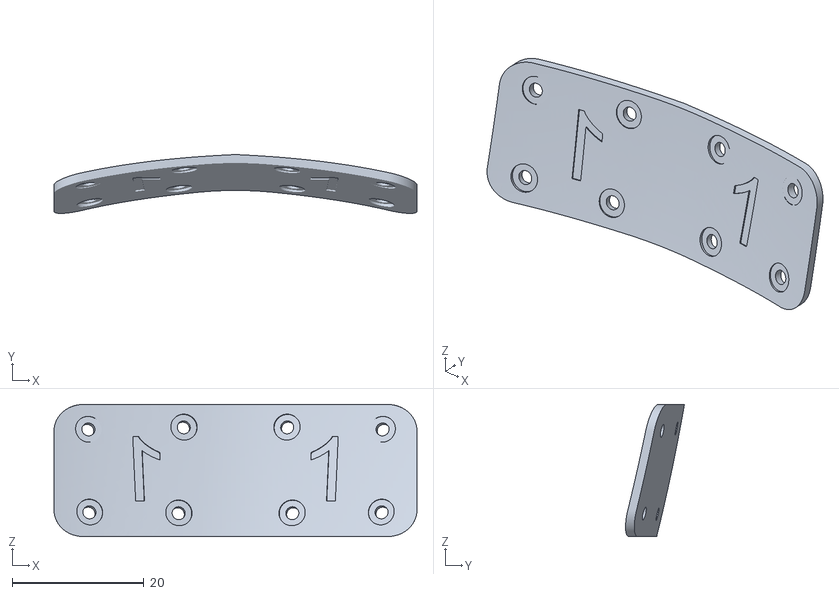
[picture p133: CAD file, 2025-01-01]
EpsilonProtogen/Frame Connectors/HelmetJoin1.stl
55.0 x 8.93 x 20.0
