coelacant1/SigmaProtogen/EpsilonProtogen/Frame/Right/RearBottomFinDisplay.stl

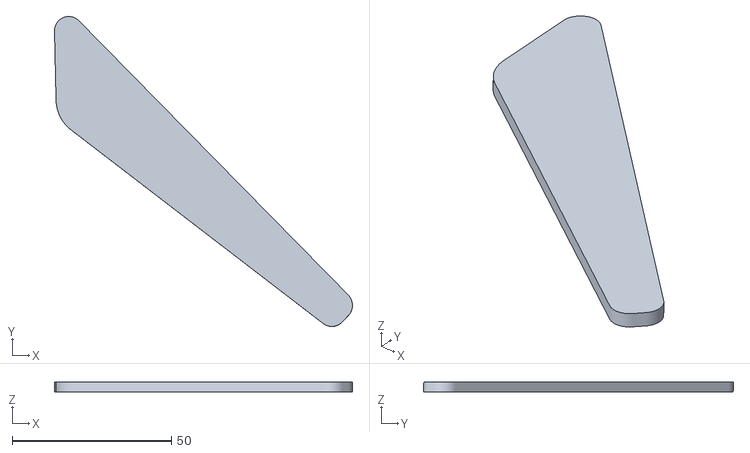
[picture p134: CAD file, 2025-01-01]
EpsilonProtogen/Frame/Right/RearBottomFinDisplay.stl
93.4 x 97.2 x 3.29
