coelacant1/SigmaProtogen/SigmaProtogen/Frame/LongFins/RearHelmet_InfillMod.stl

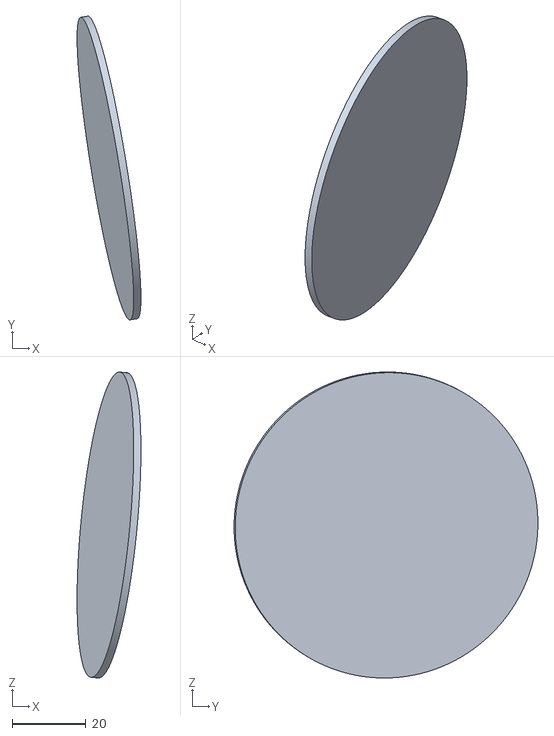
[picture p135: CAD file, 2024-06-20]
SigmaProtogen/Frame/LongFins/RearHelmet_InfillMod.stl
17.3 x 82.2 x 82.8
