coelacant1/SigmaProtogen/BetaProtogen/LED Mount MAX7219/MAX7219BottomLeft_V1-0.stl

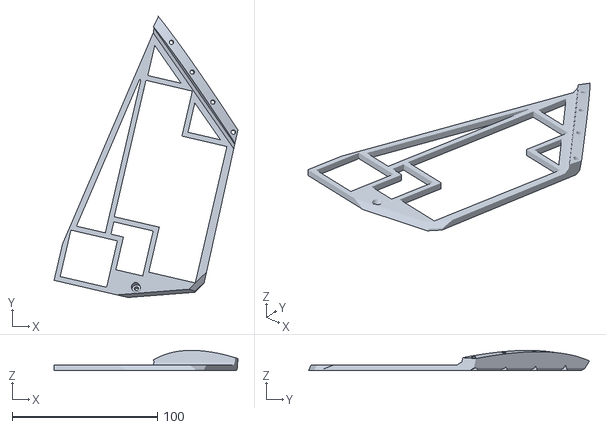
[picture p136: CAD file, 2025-01-01]
BetaProtogen/LED Mount MAX7219/MAX7219BottomLeft_V1-0.stl
126.6 x 193.4 x 14.0
