coelacant1/SigmaProtogen/BetaProtogen/LED Mount WS35/WS35BendMountSupport_V1-0.stl

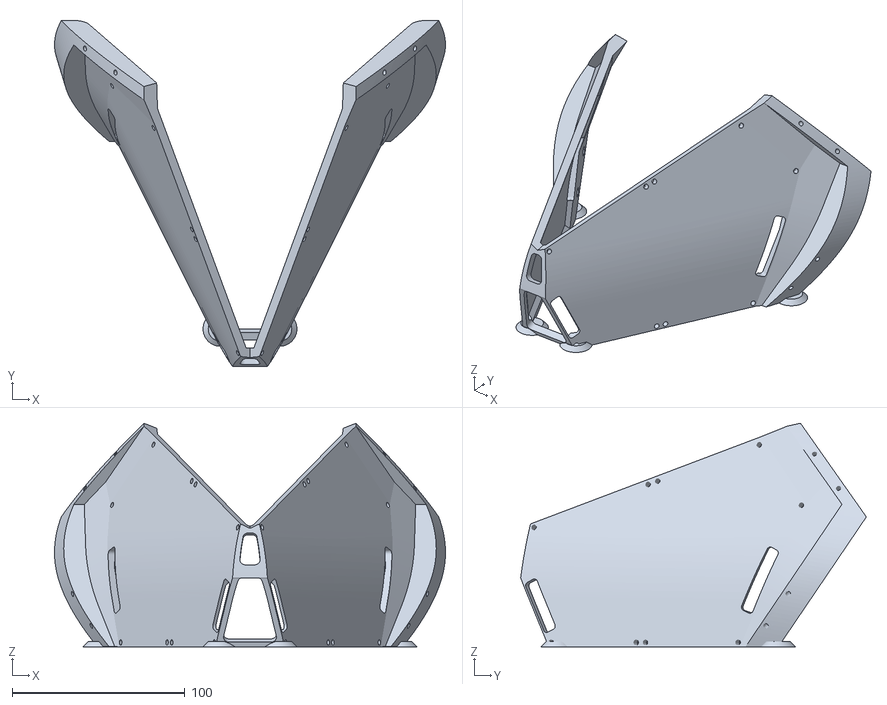
[picture p137: CAD file, 2025-01-01]
BetaProtogen/LED Mount WS35/WS35BendMountSupport_V1-0.stl
226.4 x 200.2 x 129.4
