coelacant1/SigmaProtogen/BetaProtogen/VisorMount/BotFrontMagnet.stl

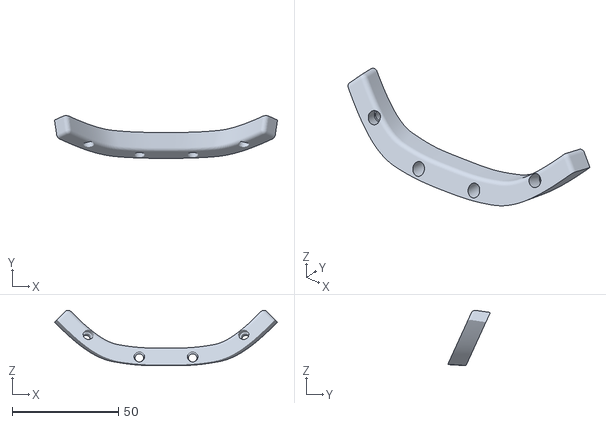
[picture p138: CAD file, 2025-01-01]
BetaProtogen/VisorMount/BotFrontMagnet.stl
104.7 x 20.1 x 26.0
