coelacant1/SigmaProtogen/DeltaProtogen/Frame/TopRightForehead_V1-0.stl

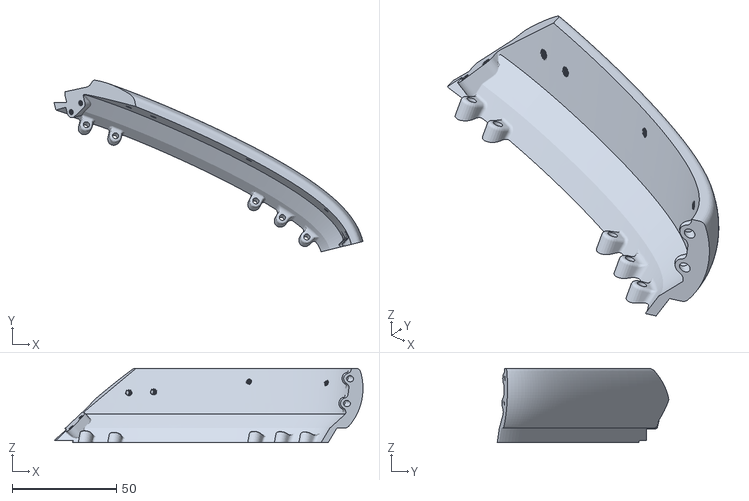
[picture p139: CAD file, 2025-01-01]
DeltaProtogen/Frame/TopRightForehead_V1-0.stl
148.4 x 82.4 x 35.7
