coelacant1/SigmaProtogen/DeltaProtogen/Visor Mounts/BottomLeftInner_V1-1.stl

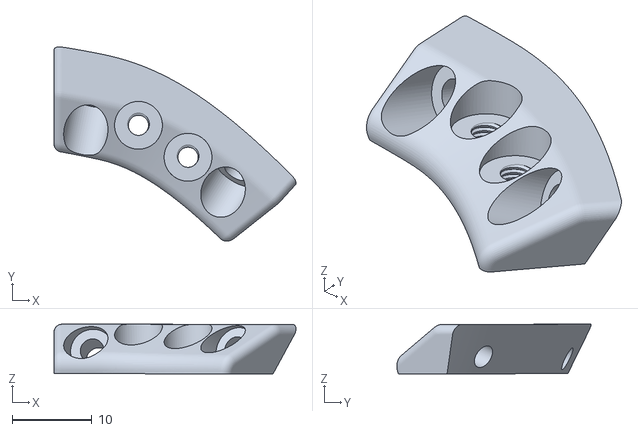
[picture p140: CAD file, 2025-01-01]
DeltaProtogen/Visor Mounts/BottomLeftInner_V1-1.stl
30.4 x 24.4 x 6.23
