coelacant1/SigmaProtogen/EpsilonProtogen/Frame Connectors/HelmetJoin3.stl

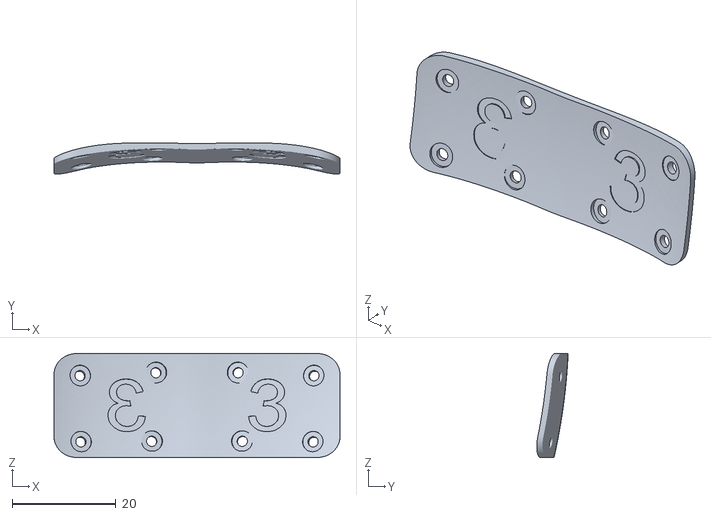
[picture p141: CAD file, 2025-01-01]
EpsilonProtogen/Frame Connectors/HelmetJoin3.stl
55.0 x 6.04 x 20.0
