coelacant1/SigmaProtogen/SigmaProtogen/Frame/ShortFins/RearHelmet.stl

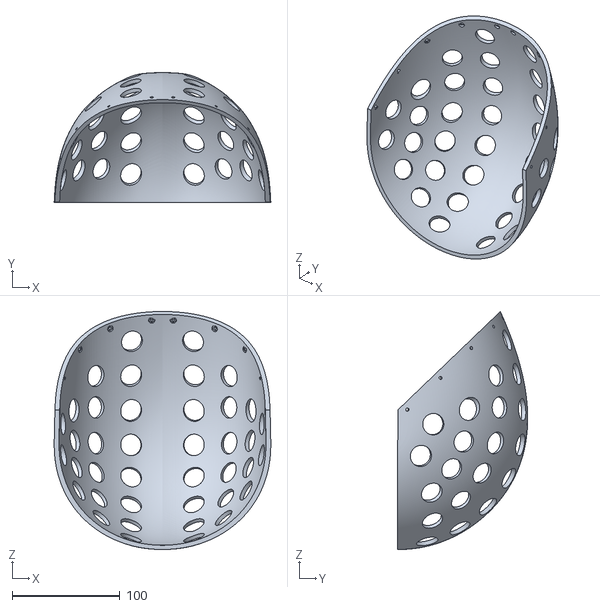
[picture p142: CAD file, 2024-05-19]
SigmaProtogen/Frame/ShortFins/RearHelmet.stl
201.3 x 121.1 x 221.1
