coelacant1/SigmaProtogen/BetaProtogen/Frame/FrameTipL_V1-0.stl

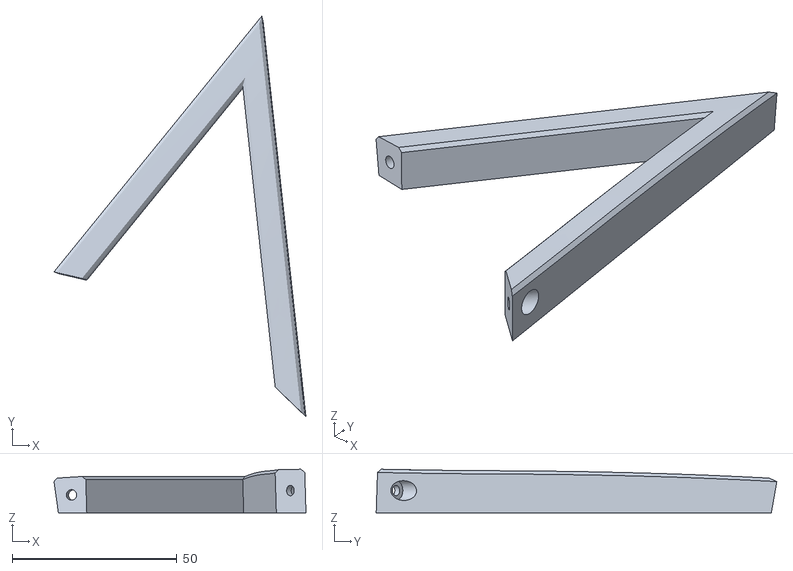
[picture p143: CAD file, 2025-01-01]
BetaProtogen/Frame/FrameTipL_V1-0.stl
76.4 x 121.5 x 13.2
