coelacant1/SigmaProtogen/BetaProtogen/Visor/Visor_V1-0.stl

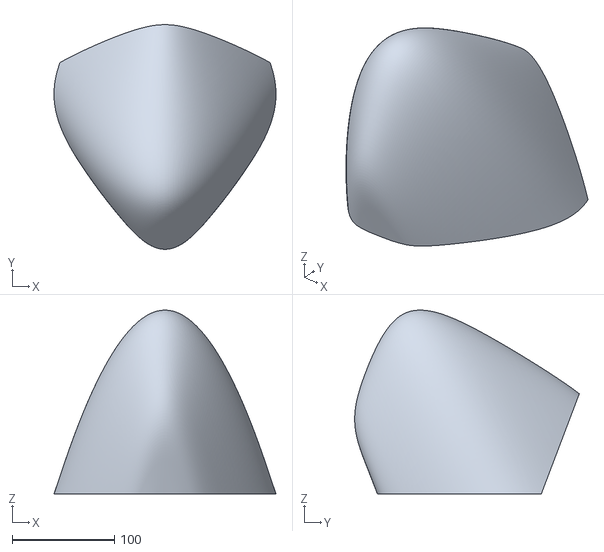
[picture p144: CAD file, 2025-01-01]
BetaProtogen/Visor/Visor_V1-0.stl
216.9 x 219.5 x 179.5
