coelacant1/SigmaProtogen/BetaProtogen/VisorMount/BotVisorMagnetMount_V1-0.stl

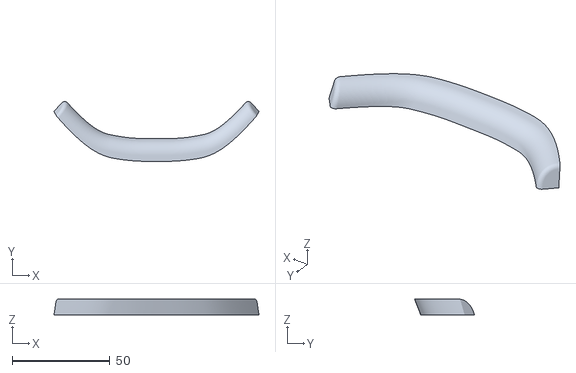
[picture p145: CAD file, 2025-01-01]
BetaProtogen/VisorMount/BotVisorMagnetMount_V1-0.stl
104.7 x 30.6 x 8.06
