coelacant1/SigmaProtogen/DeltaProtogen/Frame/RightBackHelmet_V1-0.stl

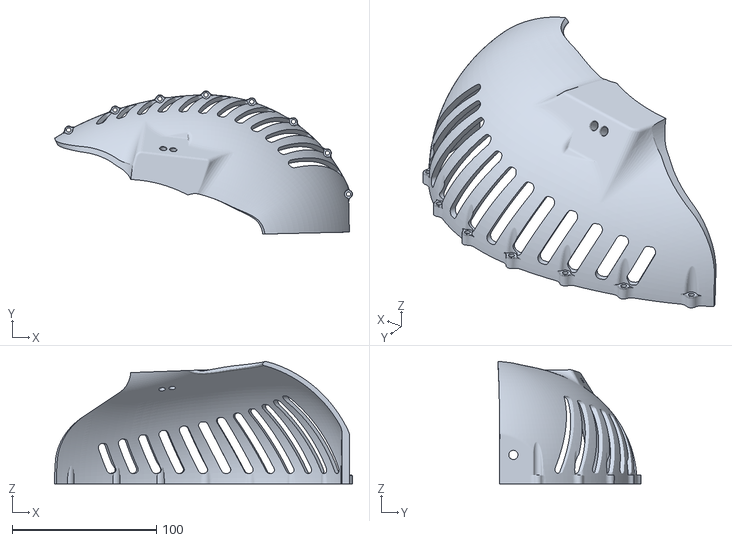
[picture p146: CAD file, 2025-01-01]
DeltaProtogen/Frame/RightBackHelmet_V1-0.stl
206.4 x 99.2 x 84.9
