coelacant1/SigmaProtogen/DeltaProtogen/Visor Mounts/VisorSupportTop.stl

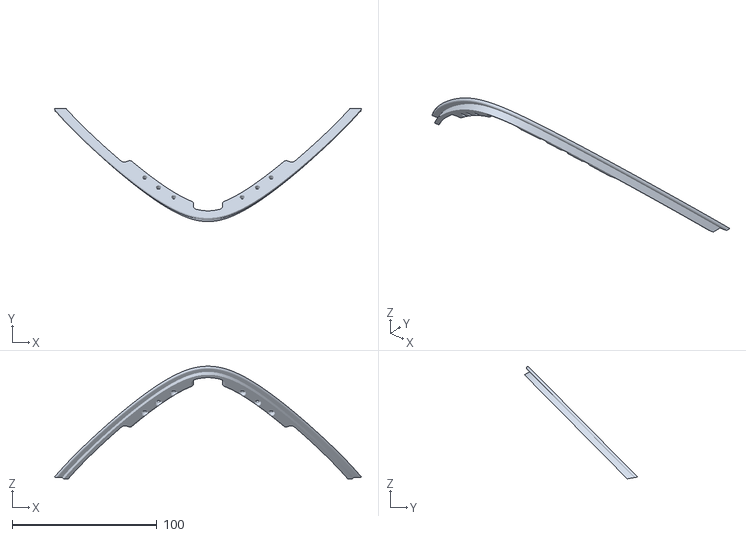
[picture p147: CAD file, 2025-01-01]
DeltaProtogen/Visor Mounts/VisorSupportTop.stl
212.3 x 78.3 x 77.9
