coelacant1/SigmaProtogen/BetaProtogen/Visor/BuckV3.stl

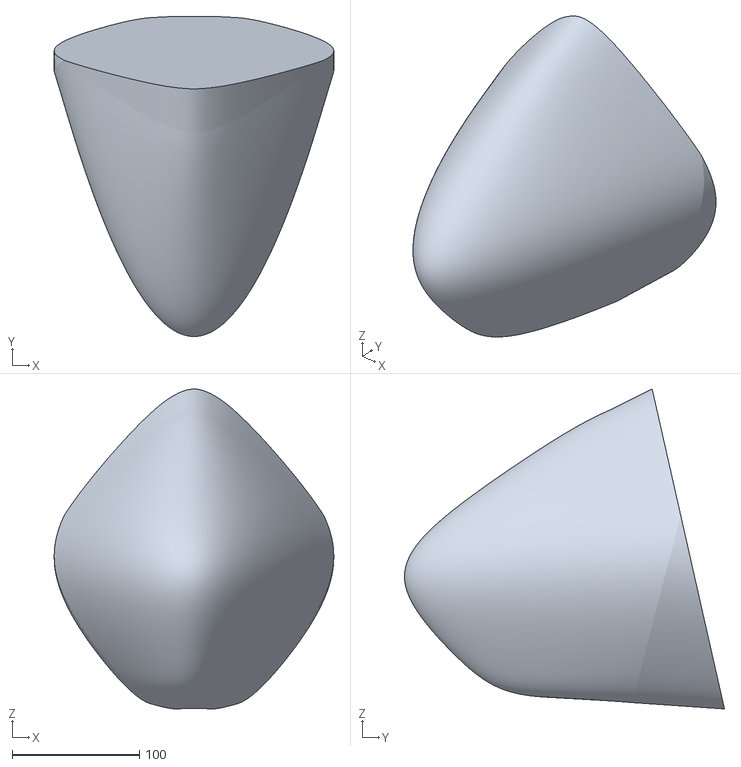
[picture p148: CAD file, 2025-01-01]
BetaProtogen/Visor/BuckV3.stl
219.7 x 251.4 x 251.4
