coelacant1/SigmaProtogen/BetaProtogen/VisorMount/TopVisorFrameMount_V1-0.stl

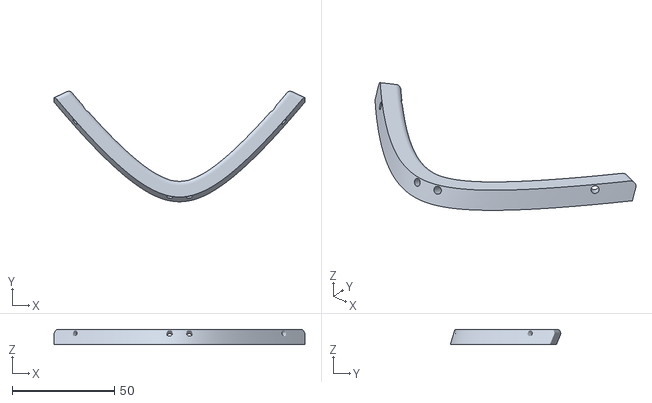
[picture p149: CAD file, 2025-01-01]
BetaProtogen/VisorMount/TopVisorFrameMount_V1-0.stl
122.6 x 54.0 x 7.54
