coelacant1/SigmaProtogen/DeltaProtogen/Frame/RightBackMid_V1-0.stl

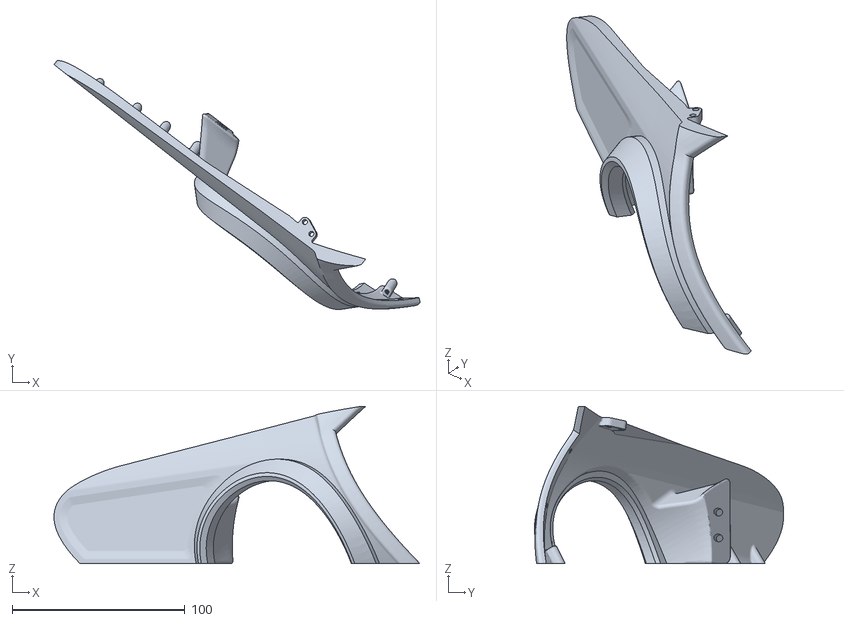
[picture p150: CAD file, 2025-01-01]
DeltaProtogen/Frame/RightBackMid_V1-0.stl
212.1 x 144.3 x 91.1
