coelacant1/SigmaProtogen/DeltaProtogen/LED Board References/ProtoTracerWiringDiagram.png

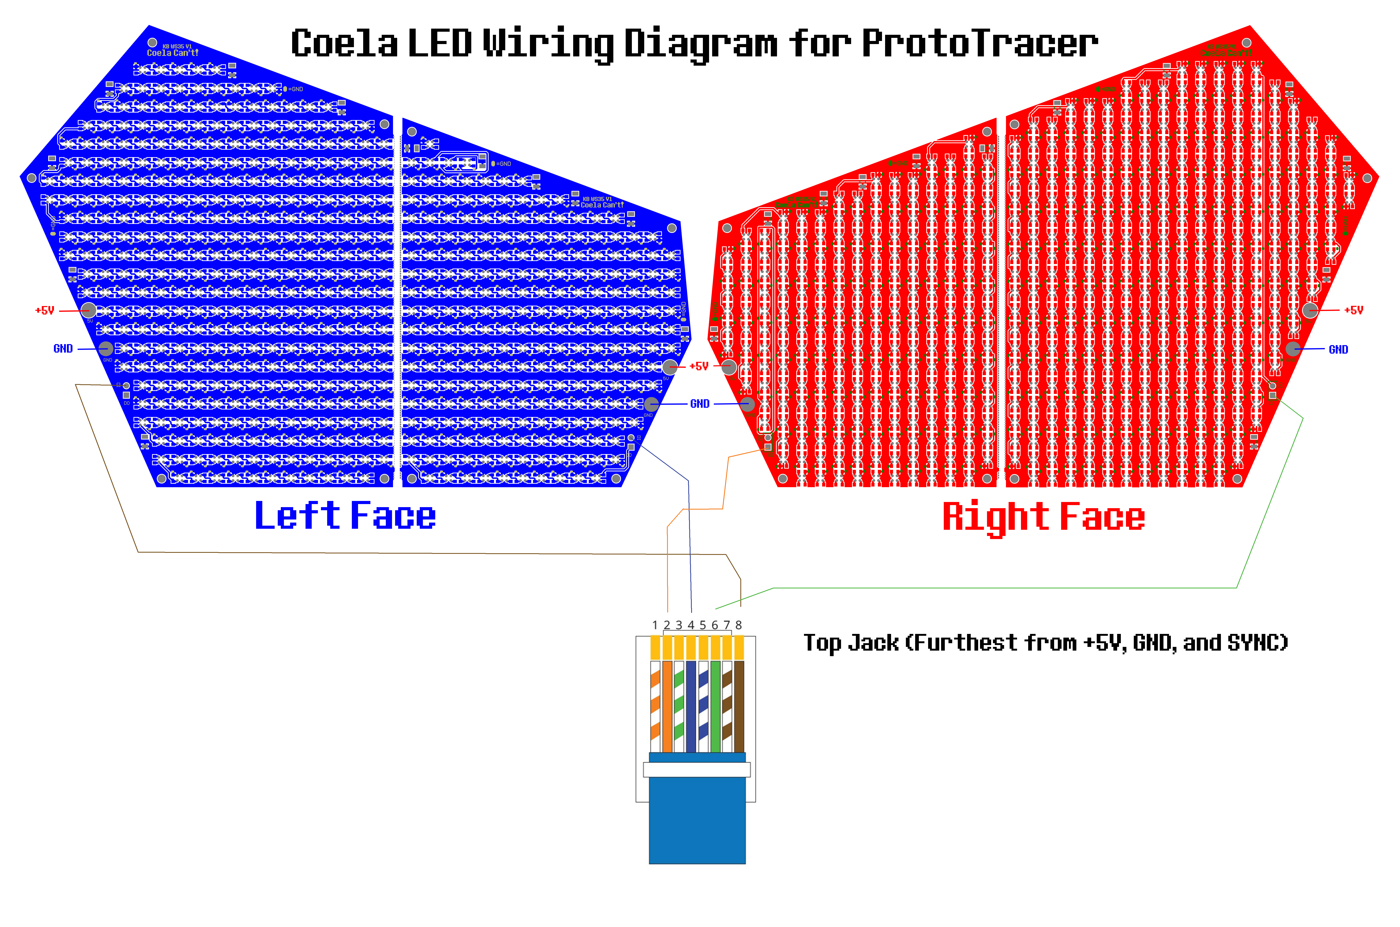
DeltaProtogen/LED Board References/ProtoTracerWiringDiagram.png
